AravinthPanch/araBeat/docs/ecg/MAX30003 Ultra-Low Power, Single-Channel Integrated Biopotential (ECG, R to R Detection) AFE - Maxim.pdf

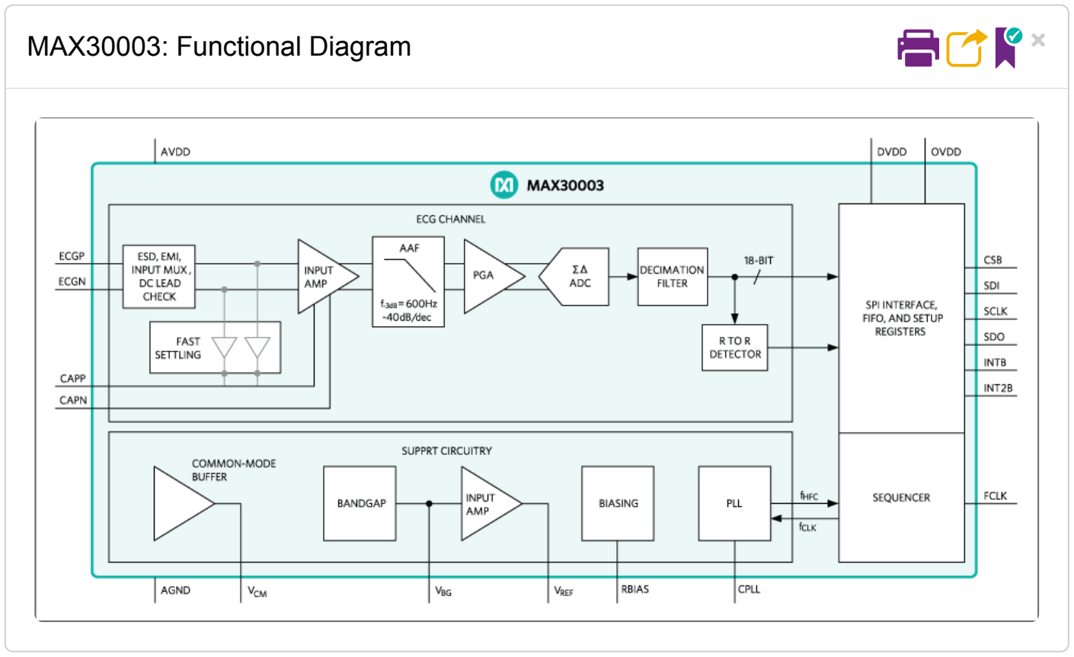
[picture p67: figure]
MAX30003: Functional Diagram
