AravinthPanch/araBeat/design/audio-rack/subwoofer-disc.jpg

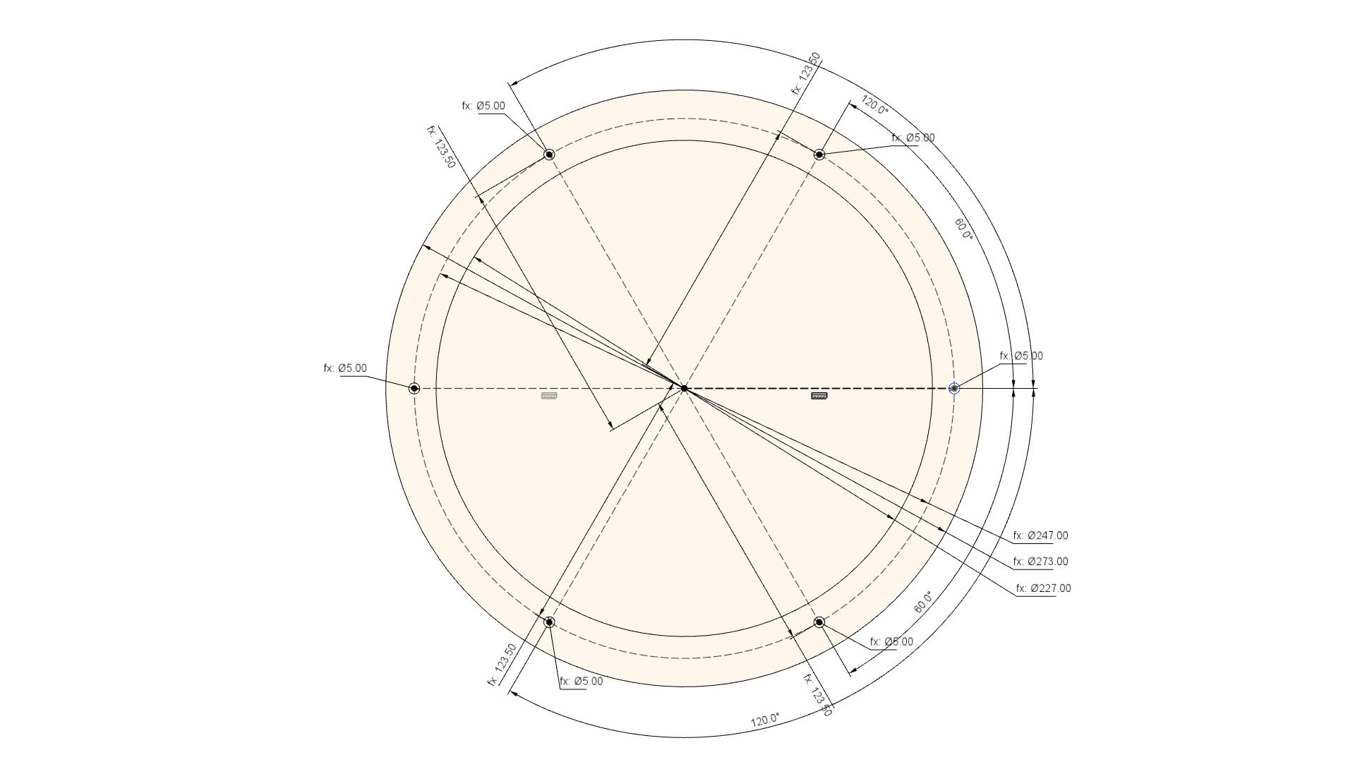
design/audio-rack/subwoofer-disc.jpg
