AravinthPanch/araBeat/design/audio-rack/tweeter-disc.jpg

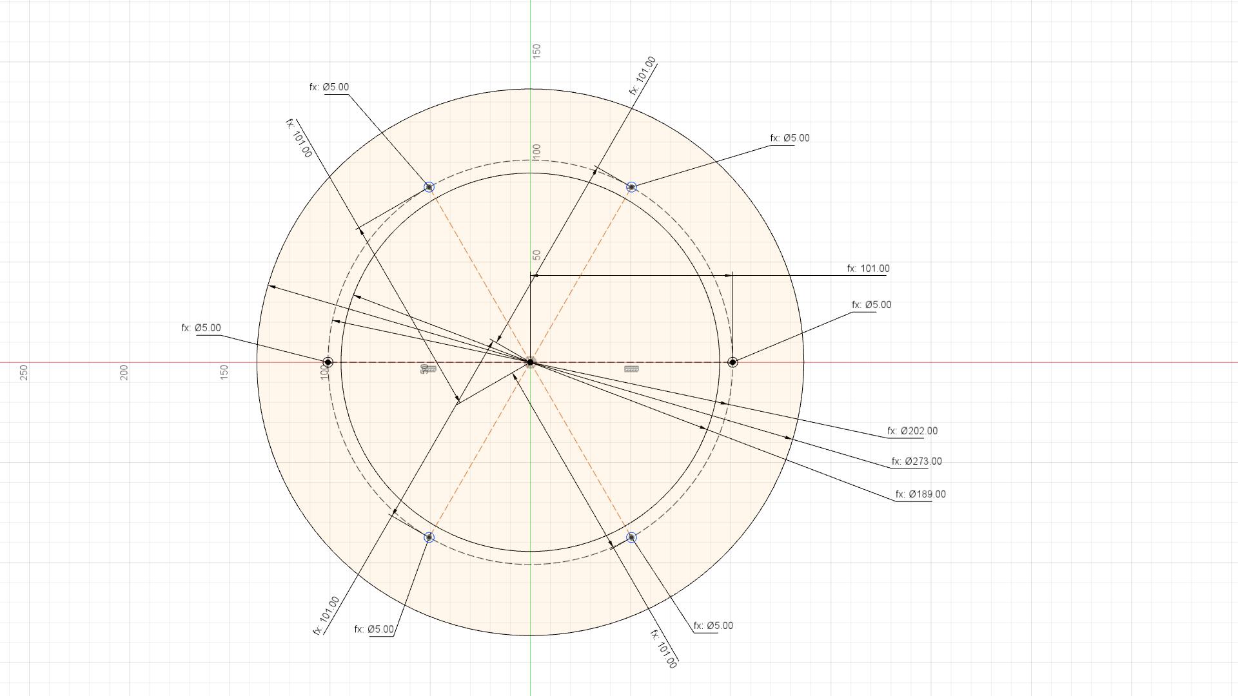
design/audio-rack/tweeter-disc.jpg
