AravinthPanch/araBeat/design/prototypes/mini-speaker-enclosure/enclosure-back.png

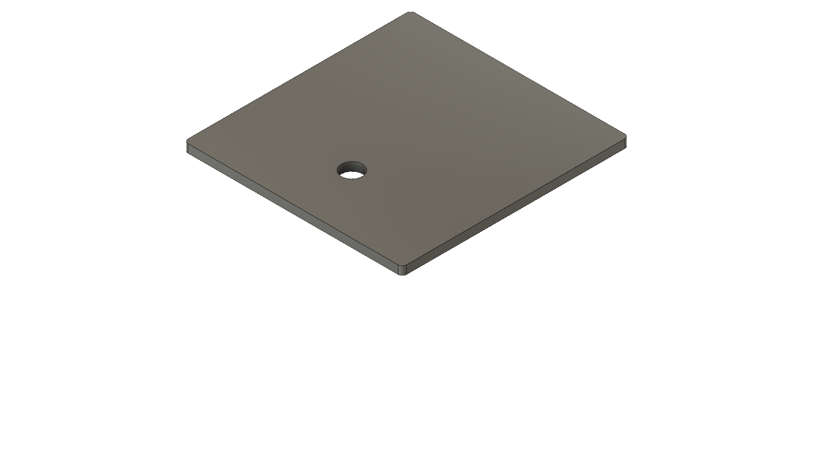
design/prototypes/mini-speaker-enclosure/enclosure-back.png
