AravinthPanch/araBeat/design/prototypes/mini-speaker-enclosure/enclosure-front.png

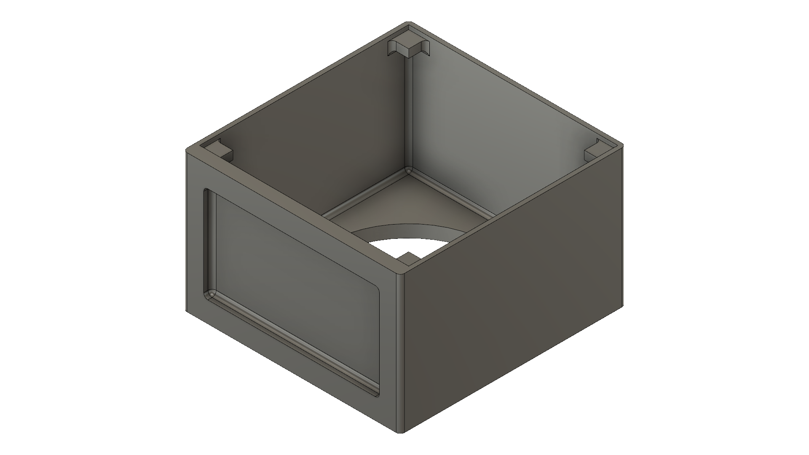
design/prototypes/mini-speaker-enclosure/enclosure-front.png
