AravinthPanch/araBeat/design/prototypes/mini-speaker-enclosure/enclosure.jpg

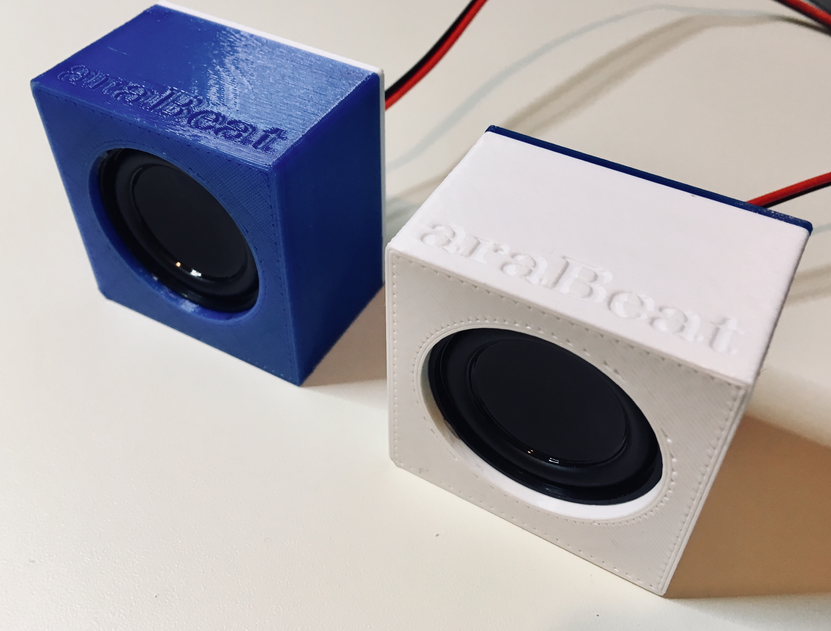
design/prototypes/mini-speaker-enclosure/enclosure.jpg
