AravinthPanch/araBeat/design/sensor-frontend/design-4-draft-chamfer/20181226_Arabeat_Draft_Hollow_preview.JPG

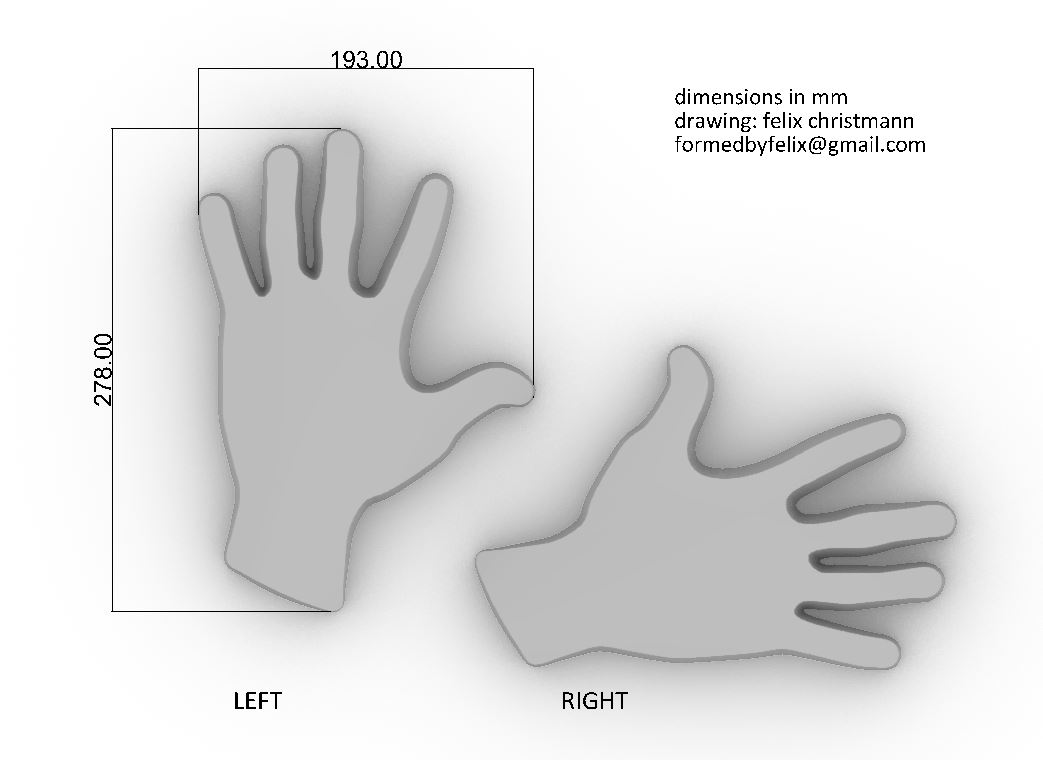
design/sensor-frontend/design-4-draft-chamfer/20181226_Arabeat_Draft_Hollow_preview.JPG
