AravinthPanch/araBeat/design/system-design/images/led-strip.png

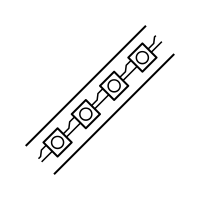
design/system-design/images/led-strip.png
