AravinthPanch/araBeat/design/system-design/system-2.png

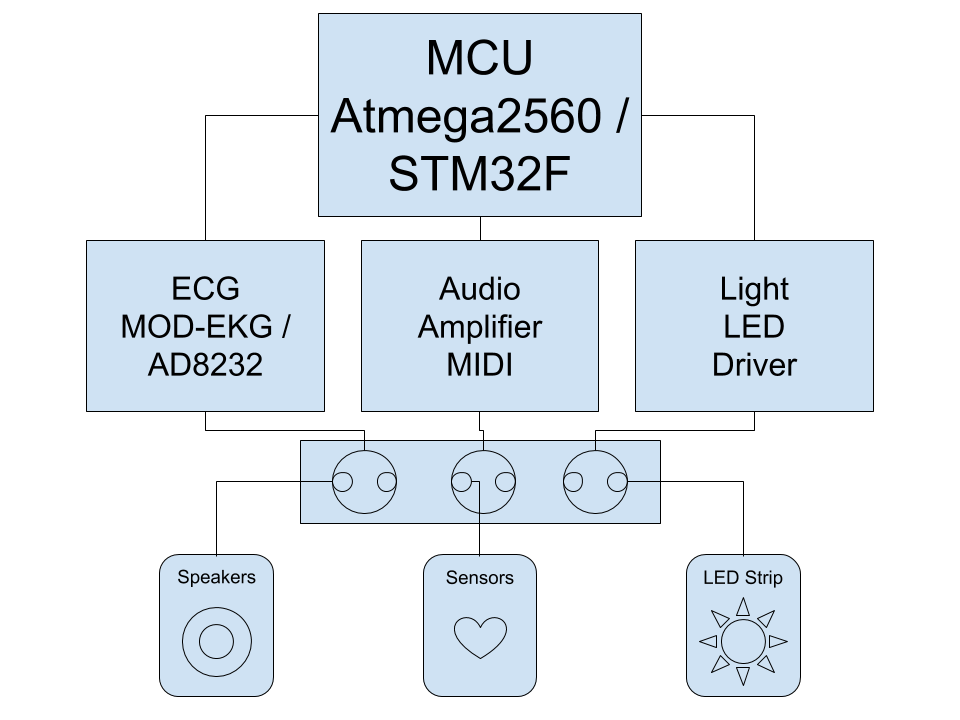
design/system-design/system-2.png
