AravinthPanch/araBeat/docs/connectors/031-203-RFX_1_SPL.jpg

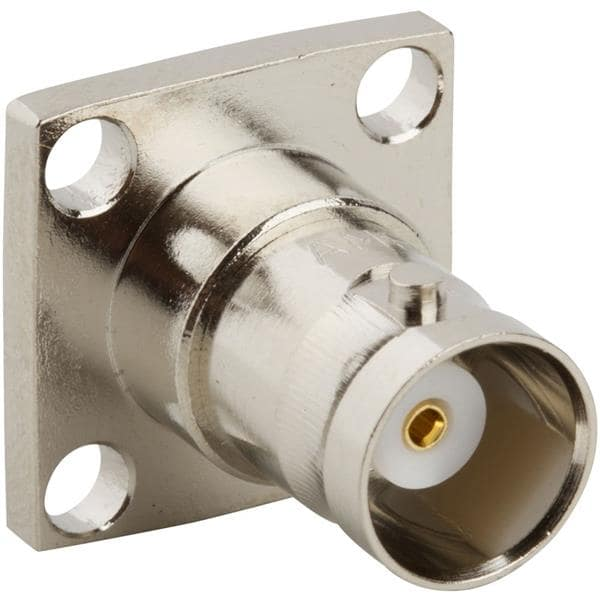
docs/connectors/031-203-RFX_1_SPL.jpg
