AravinthPanch/araBeat/docs/connectors/61caJ1zhngL._SX569_.jpg

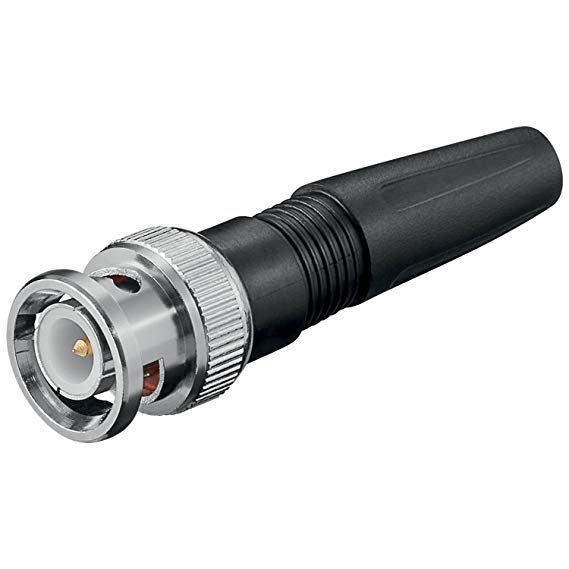
docs/connectors/61caJ1zhngL._SX569_.jpg
