AravinthPanch/araBeat/docs/connectors/BNC_RF_jack_PCB_SPL.jpg

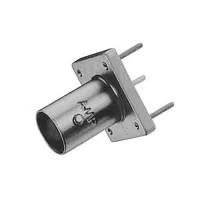
docs/connectors/BNC_RF_jack_PCB_SPL.jpg
