AravinthPanch/araBeat/docs/connectors/inhouse_vb334n_t.jpg

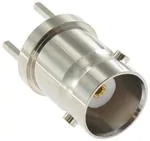
docs/connectors/inhouse_vb334n_t.jpg
