AravinthPanch/araBeat/docs/connectors/weatherproof-cable-gland-1.jpg

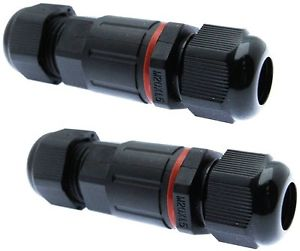
docs/connectors/weatherproof-cable-gland-1.jpg
