AravinthPanch/araBeat/docs/connectors/weatherproof-cable-gland-2.jpg

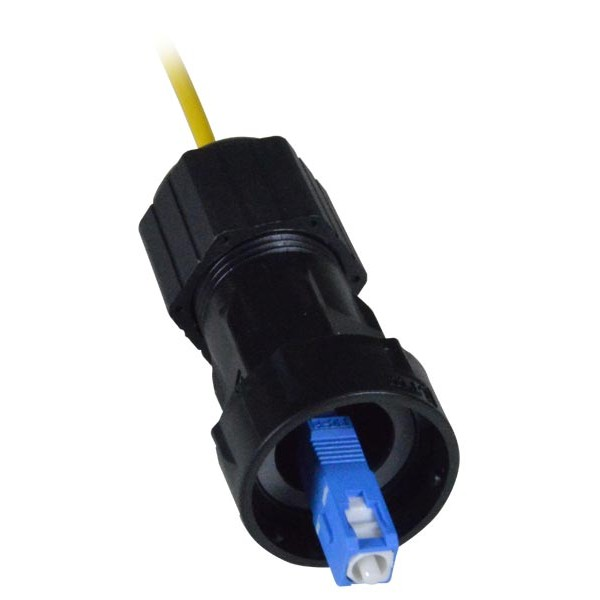
docs/connectors/weatherproof-cable-gland-2.jpg
