AravinthPanch/araBeat/docs/ecg/processing.png

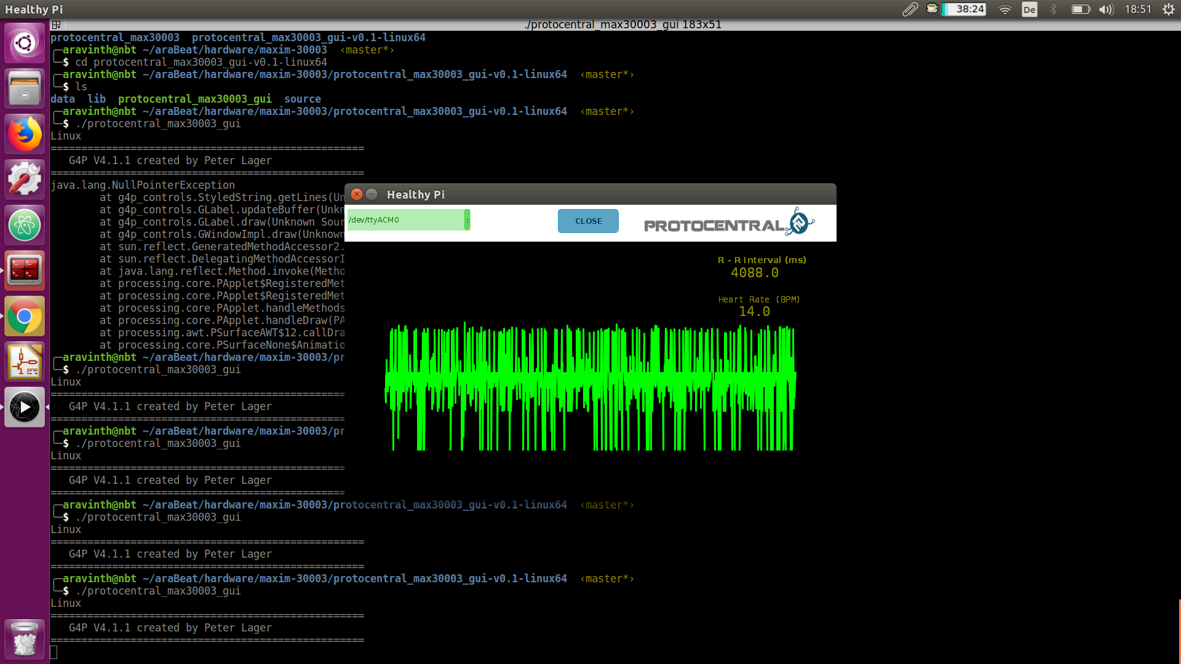
docs/ecg/processing.png
