AravinthPanch/araBeat/docs/enclosure/enclosure-1.jpg

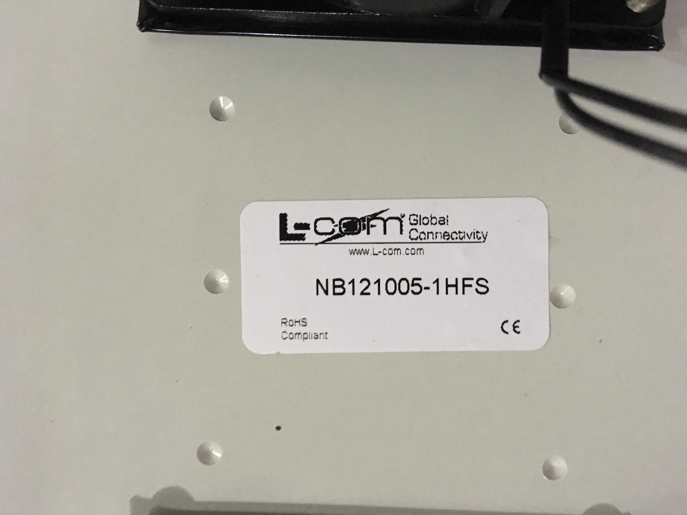
docs/enclosure/enclosure-1.jpg
