AravinthPanch/araBeat/docs/enclosure/enclosure-2.jpg

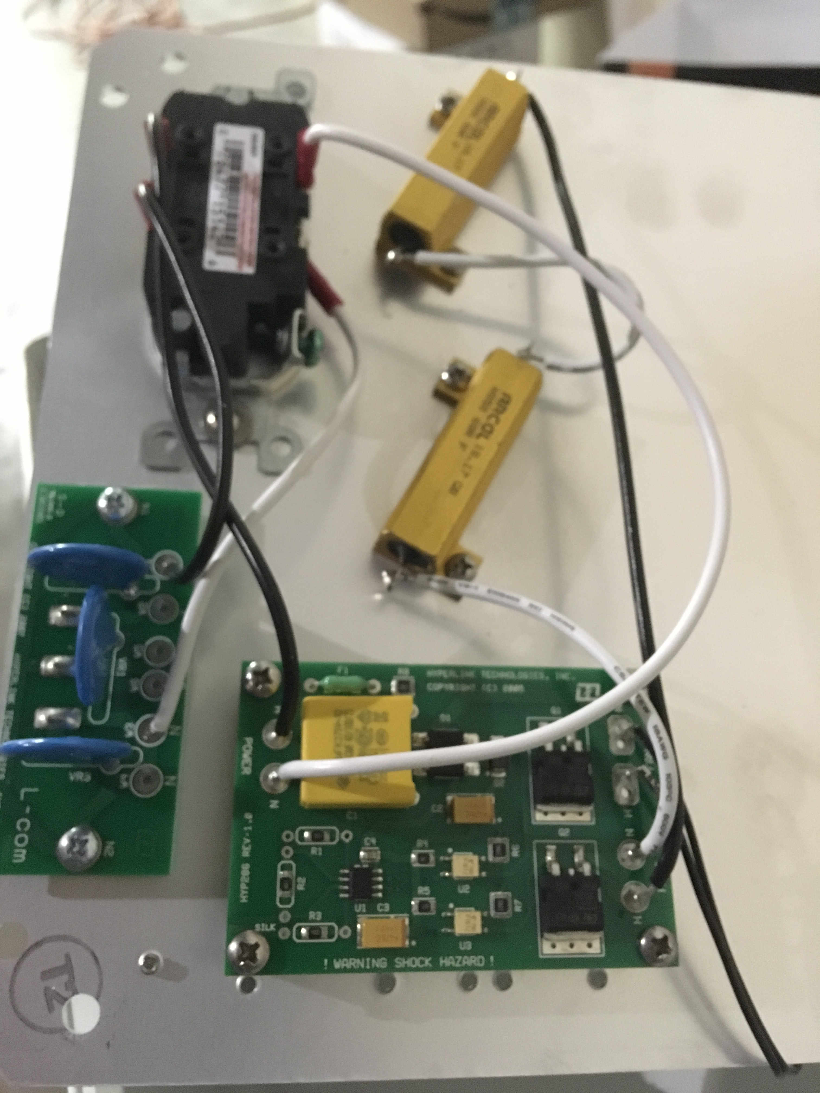
docs/enclosure/enclosure-2.jpg
