AravinthPanch/araBeat/docs/enclosure/enclosure-3.jpg

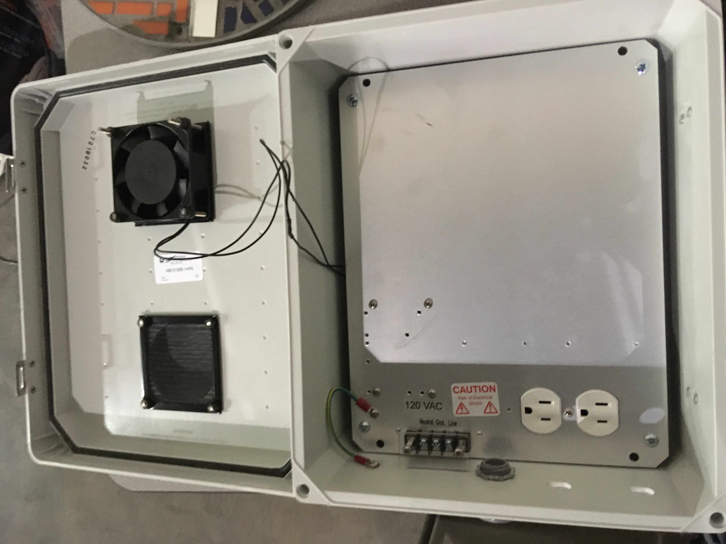
docs/enclosure/enclosure-3.jpg
