AravinthPanch/araBeat/docs/psu/linear-power.jpg

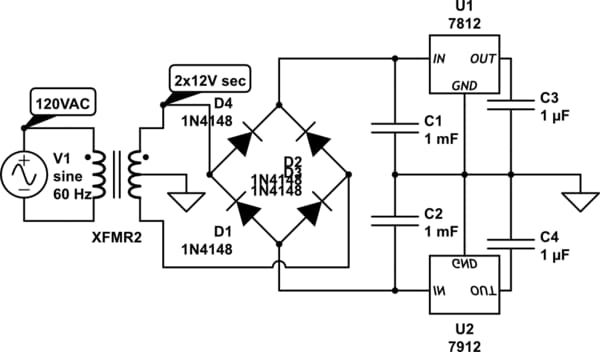
docs/psu/linear-power.jpg
