AravinthPanch/araBeat/hardware/-resources/design-rules/design-rules-1.png

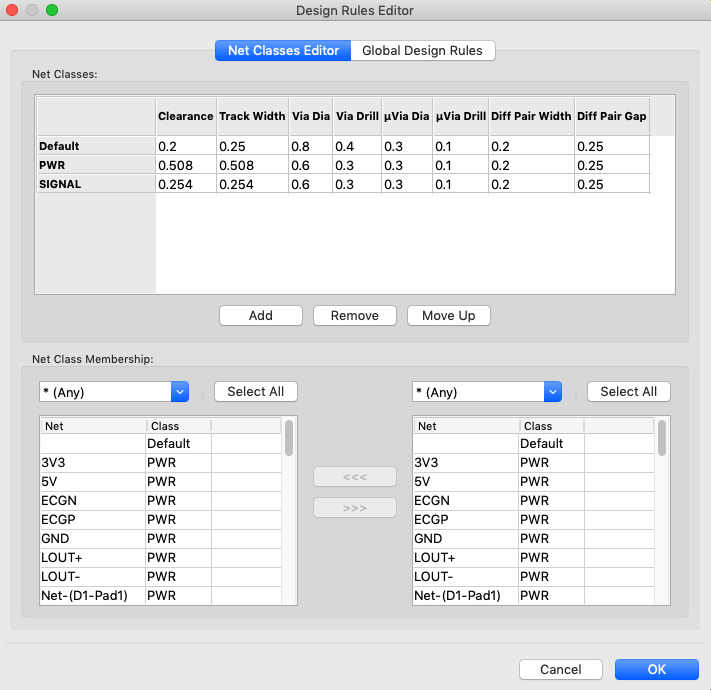
hardware/-resources/design-rules/design-rules-1.png
