AravinthPanch/araBeat/hardware/-resources/design-rules/design-rules-2.png

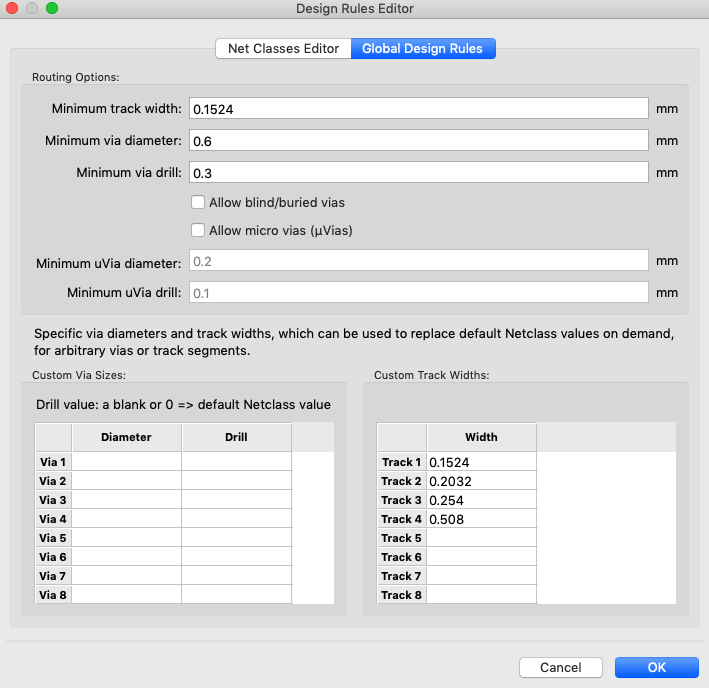
hardware/-resources/design-rules/design-rules-2.png
