AravinthPanch/araBeat/hardware/-resources/edgecut-silkscreen/inspirations/cassette-1.jpg

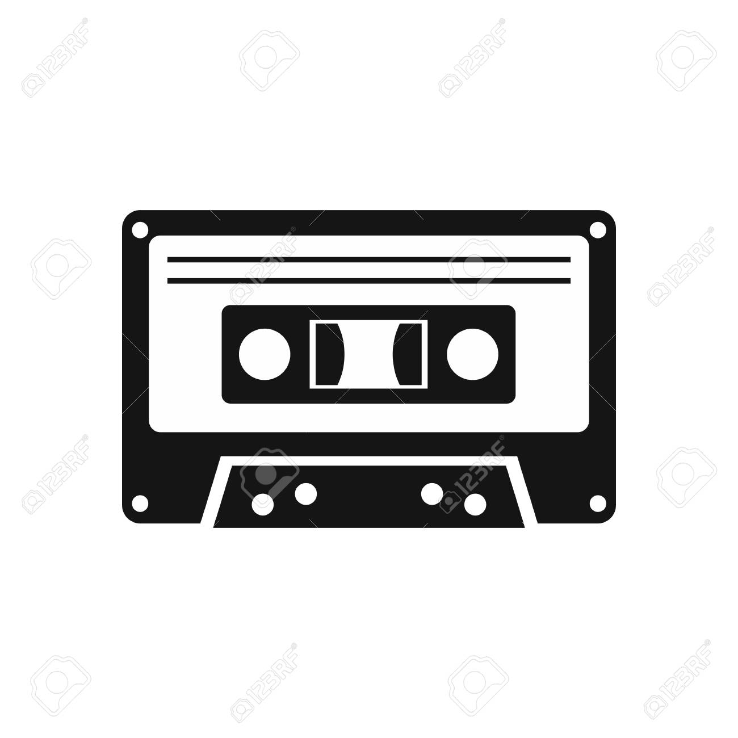
hardware/-resources/edgecut-silkscreen/inspirations/cassette-1.jpg
