AravinthPanch/araBeat/hardware/-resources/edgecut-silkscreen/inspirations/cassette-1.png

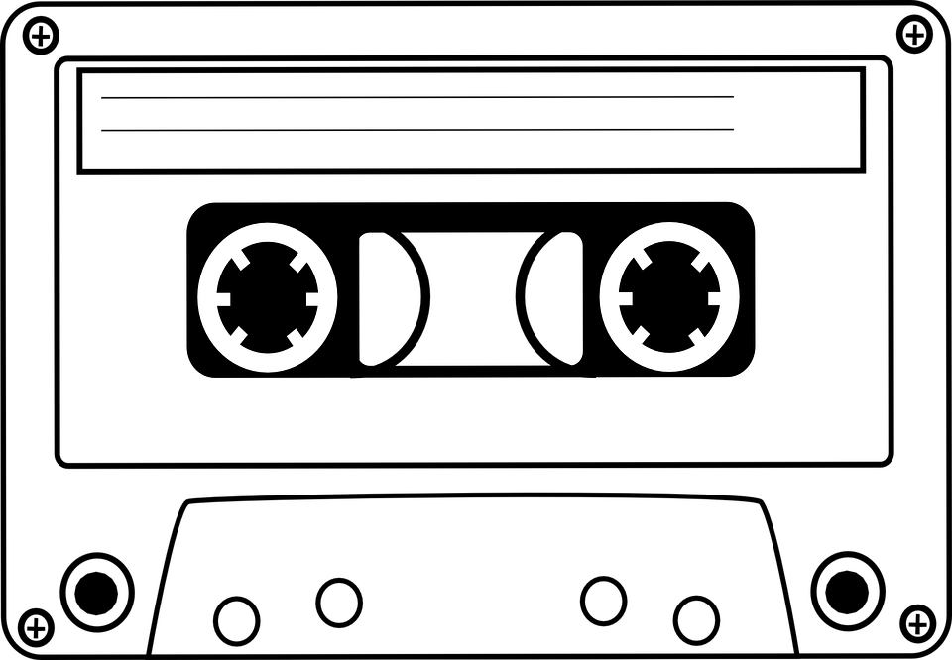
hardware/-resources/edgecut-silkscreen/inspirations/cassette-1.png
