AravinthPanch/araBeat/hardware/-resources/edgecut-silkscreen/inspirations/cassette-2.jpg

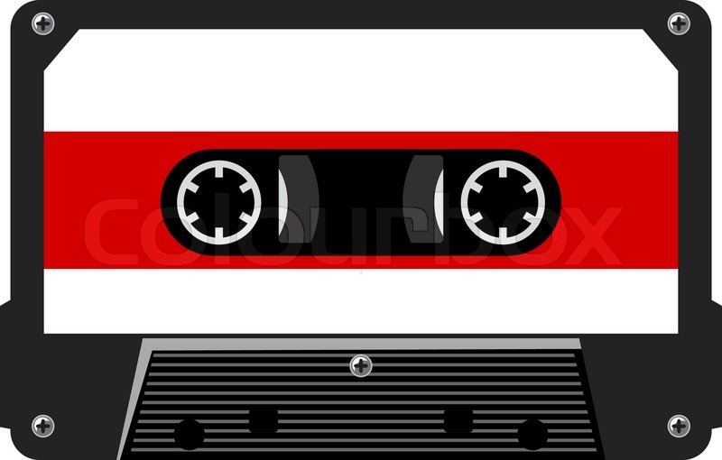
hardware/-resources/edgecut-silkscreen/inspirations/cassette-2.jpg
