AravinthPanch/araBeat/hardware/-resources/edgecut-silkscreen/inspirations/modular-1.jpg

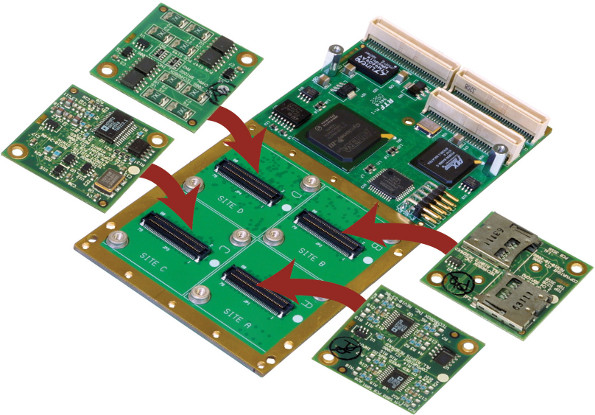
hardware/-resources/edgecut-silkscreen/inspirations/modular-1.jpg
