AravinthPanch/araBeat/hardware/-resources/edgecut-silkscreen/inspirations/modular-2.jpg

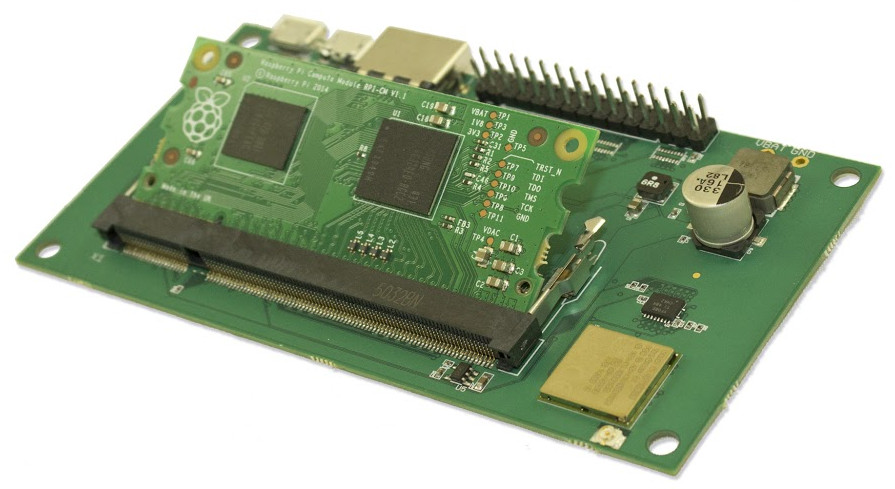
hardware/-resources/edgecut-silkscreen/inspirations/modular-2.jpg
