AravinthPanch/araBeat/hardware/-resources/edgecut-silkscreen/inspirations/modular-3.jpg

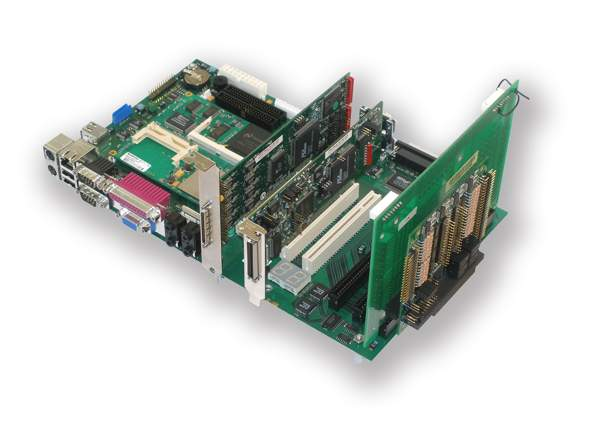
hardware/-resources/edgecut-silkscreen/inspirations/modular-3.jpg
