AravinthPanch/araBeat/hardware/-resources/edgecut-silkscreen/inspirations/retro-console-1.jpg

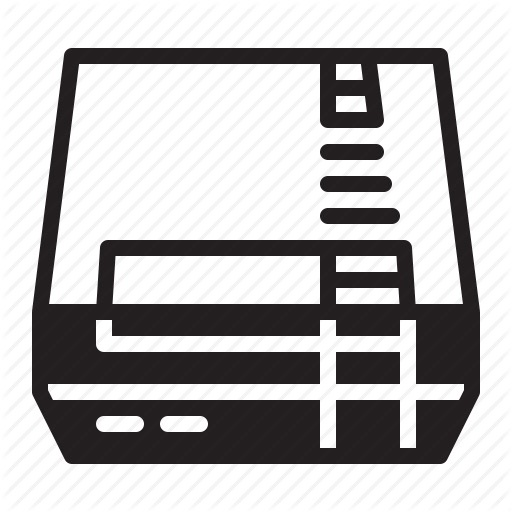
hardware/-resources/edgecut-silkscreen/inspirations/retro-console-1.jpg
