AravinthPanch/araBeat/hardware/-resources/edgecut-silkscreen/inspirations/retro-console-2.jpg

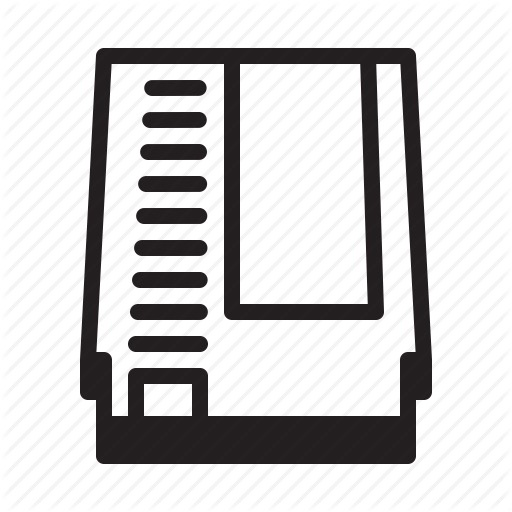
hardware/-resources/edgecut-silkscreen/inspirations/retro-console-2.jpg
