AravinthPanch/araBeat/hardware/-resources/edgecut-silkscreen/inspirations/retro-console-3.jpg

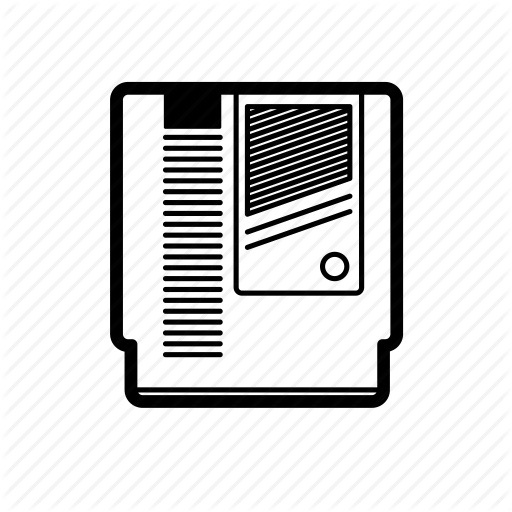
hardware/-resources/edgecut-silkscreen/inspirations/retro-console-3.jpg
