AravinthPanch/araBeat/hardware/-resources/edgecut-silkscreen/inspirations/retro-console-4.jpg

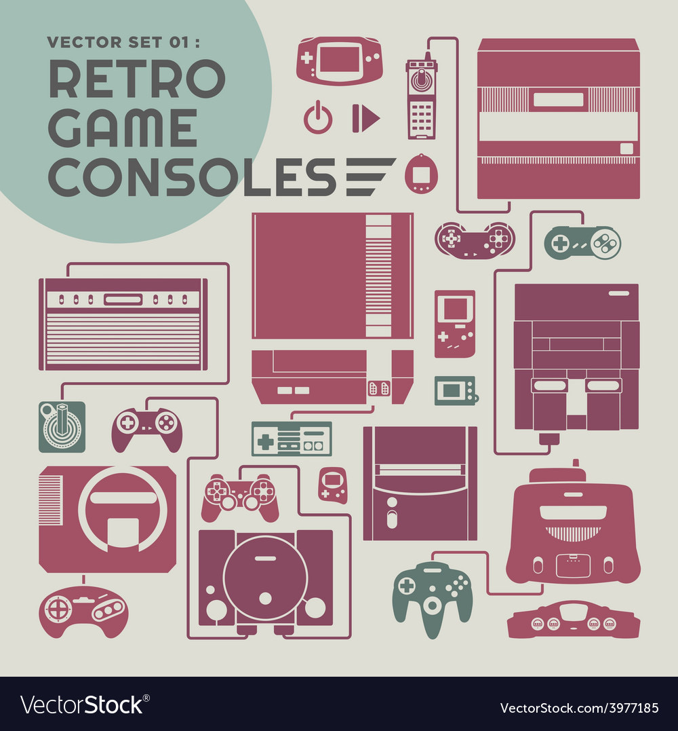
hardware/-resources/edgecut-silkscreen/inspirations/retro-console-4.jpg
