AravinthPanch/araBeat/hardware/-resources/edgecut-silkscreen/inspirations/retro-console-5.jpg

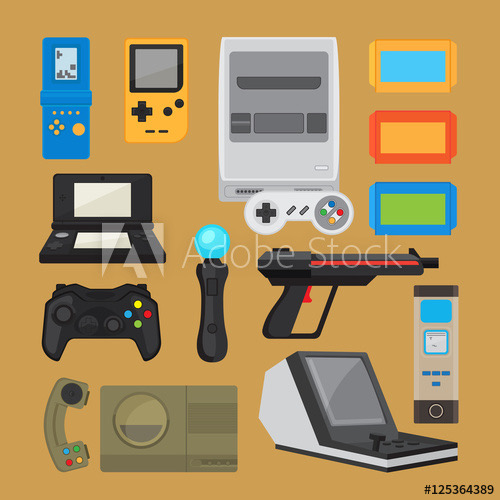
hardware/-resources/edgecut-silkscreen/inspirations/retro-console-5.jpg
