AravinthPanch/araBeat/hardware/-resources/edgecut-silkscreen/inspirations/retro-console-6.jpg

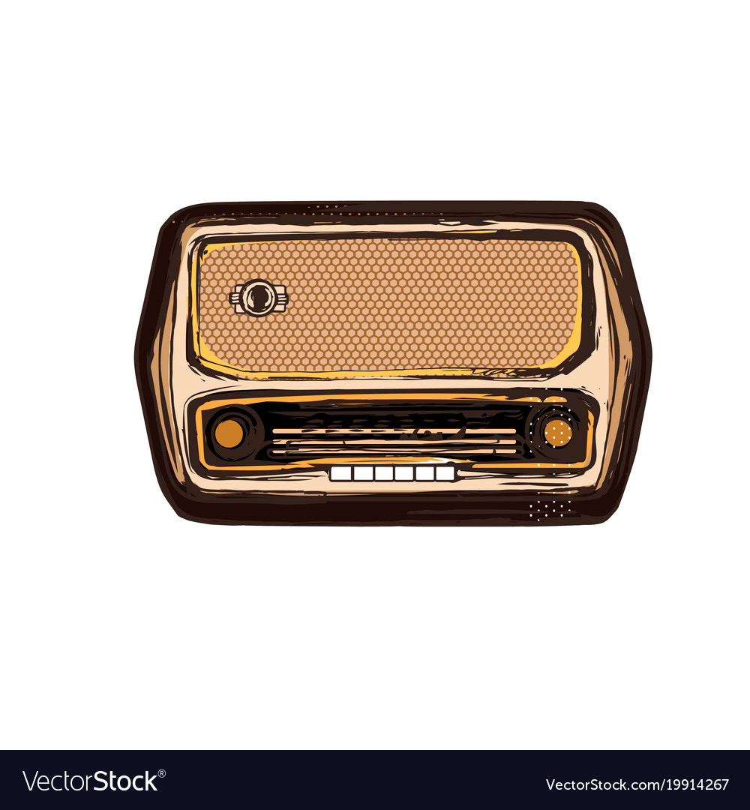
hardware/-resources/edgecut-silkscreen/inspirations/retro-console-6.jpg
