AravinthPanch/araBeat/hardware/-resources/edgecut-silkscreen/inspirations/retro-console-7.jpg

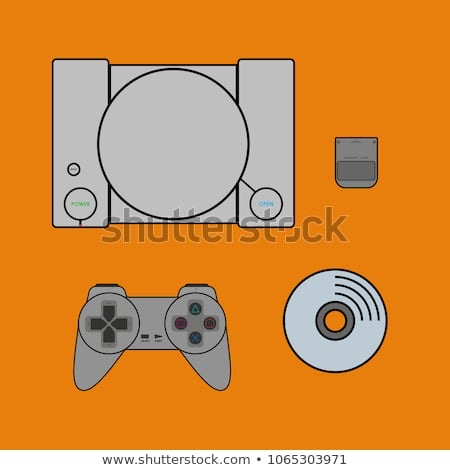
hardware/-resources/edgecut-silkscreen/inspirations/retro-console-7.jpg
