AravinthPanch/araBeat/hardware/-resources/misc/smd-footprint.png

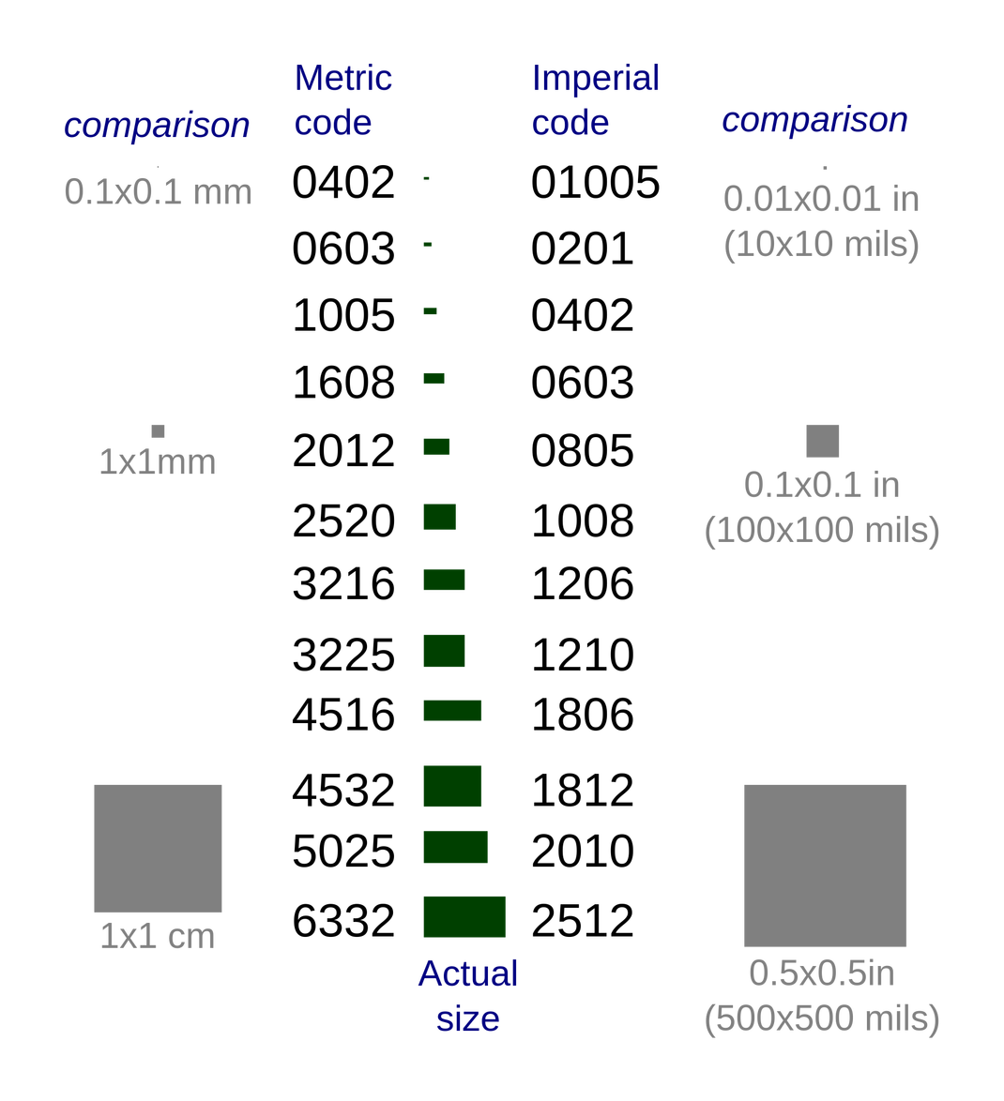
hardware/-resources/misc/smd-footprint.png
