AravinthPanch/araBeat/hardware/-resources/pinout/arduino-nano-pinout.png

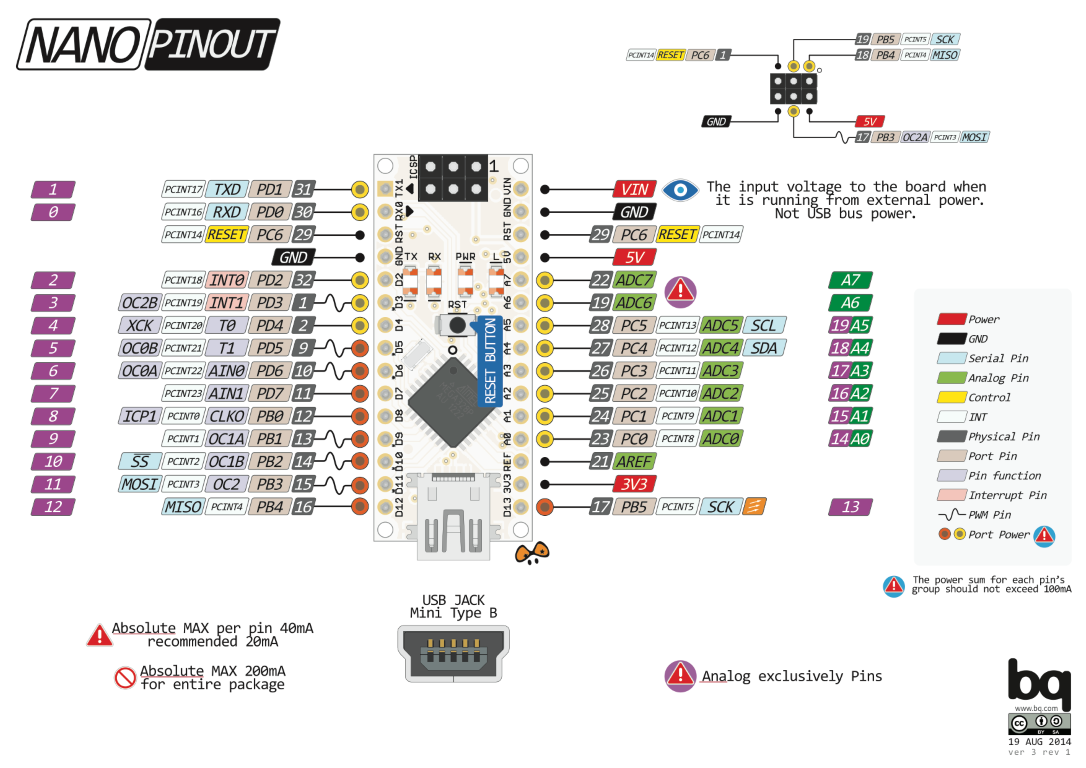
hardware/-resources/pinout/arduino-nano-pinout.png
