AravinthPanch/araBeat/hardware/-resources/pinout/dsp.png

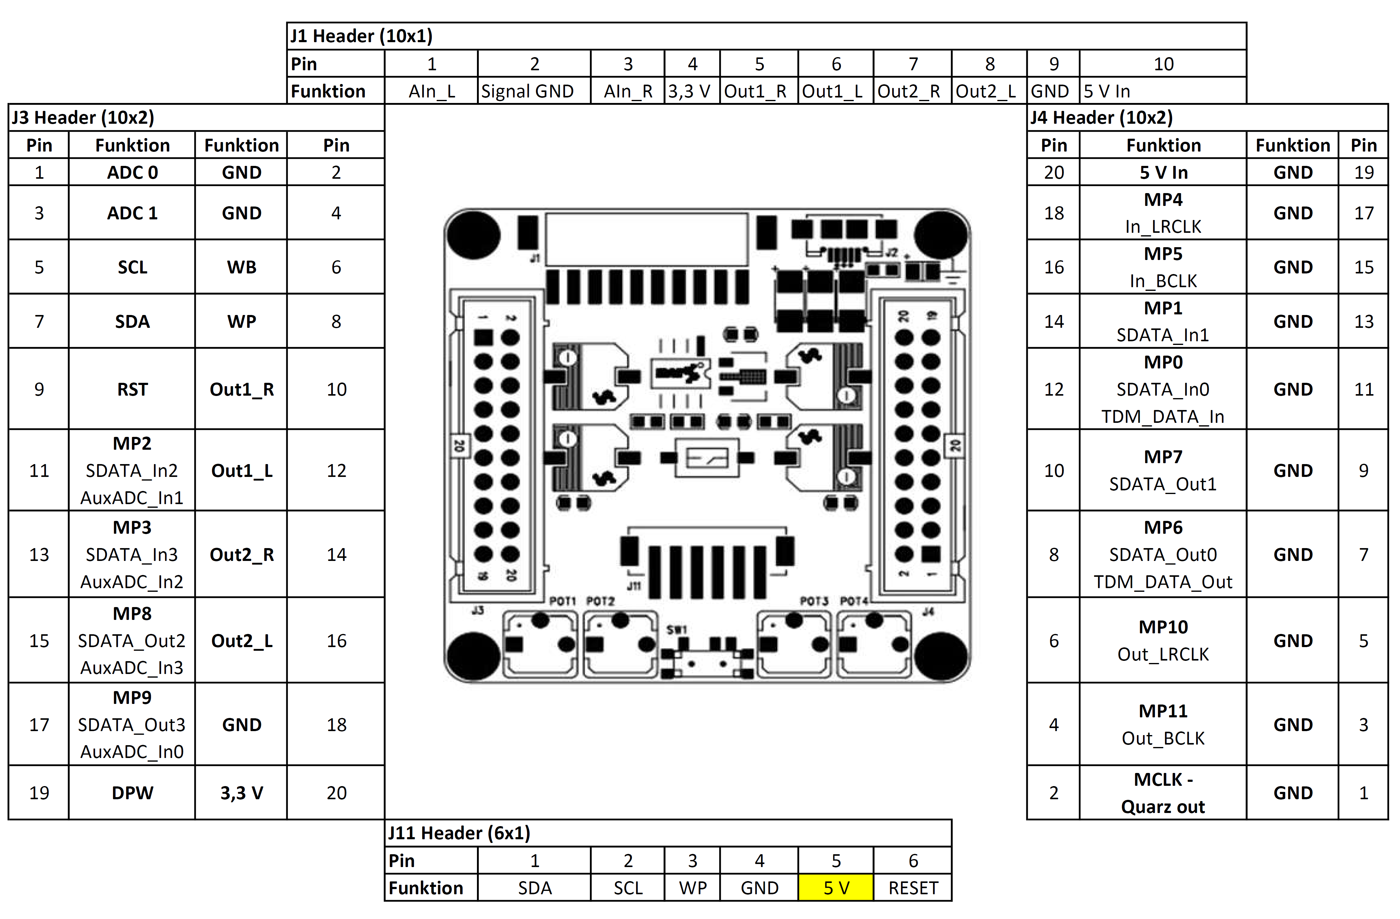
hardware/-resources/pinout/dsp.png
