AravinthPanch/araBeat/hardware/-resources/pinout/rca-interface.png

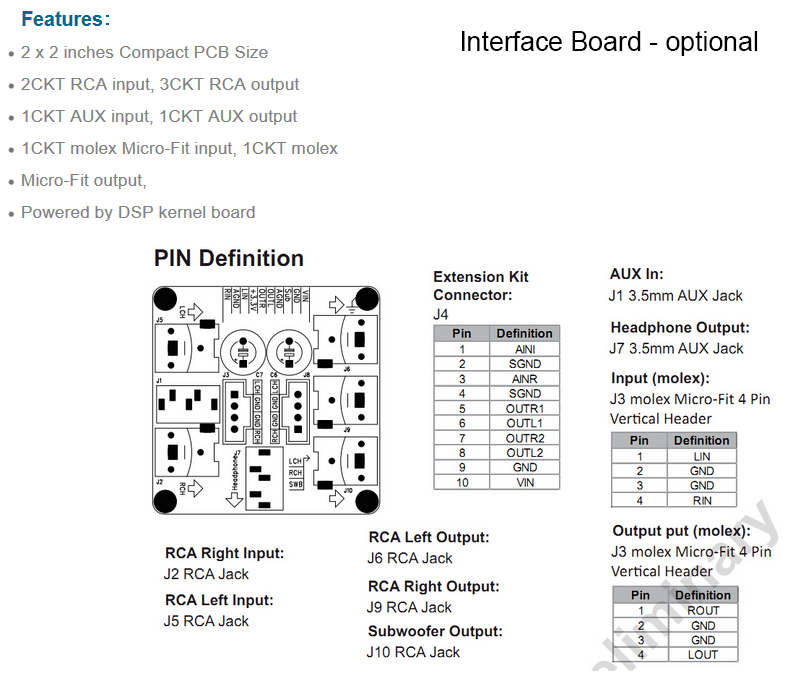
hardware/-resources/pinout/rca-interface.png
