AravinthPanch/araBeat/hardware/-resources/seeed-dfm/gerber-1.png

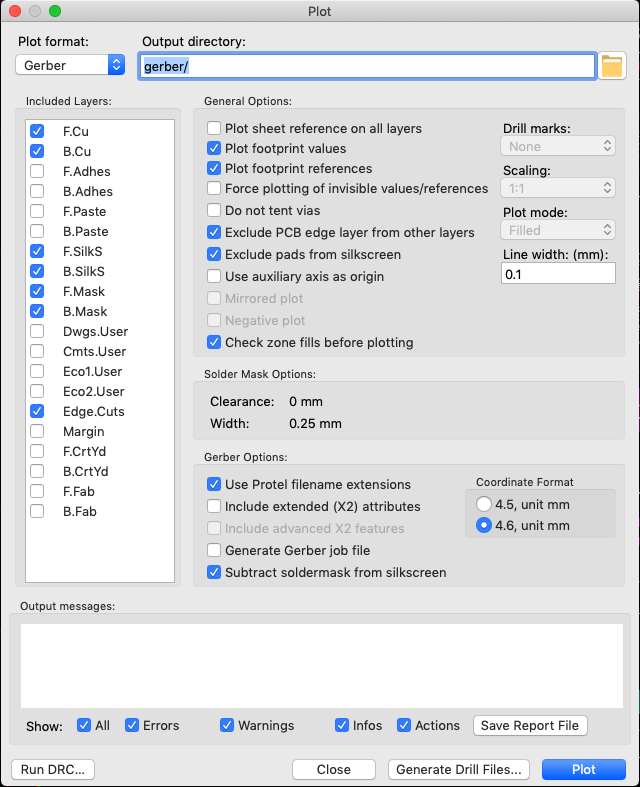
hardware/-resources/seeed-dfm/gerber-1.png
