AravinthPanch/araBeat/hardware/-resources/seeed-dfm/gerber-2.png

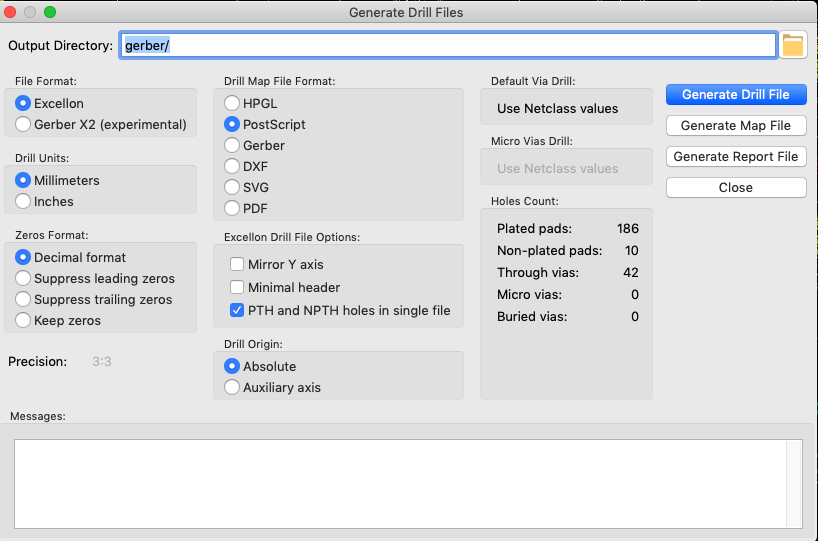
hardware/-resources/seeed-dfm/gerber-2.png
