AravinthPanch/araBeat/images/audio/audio-1.jpg

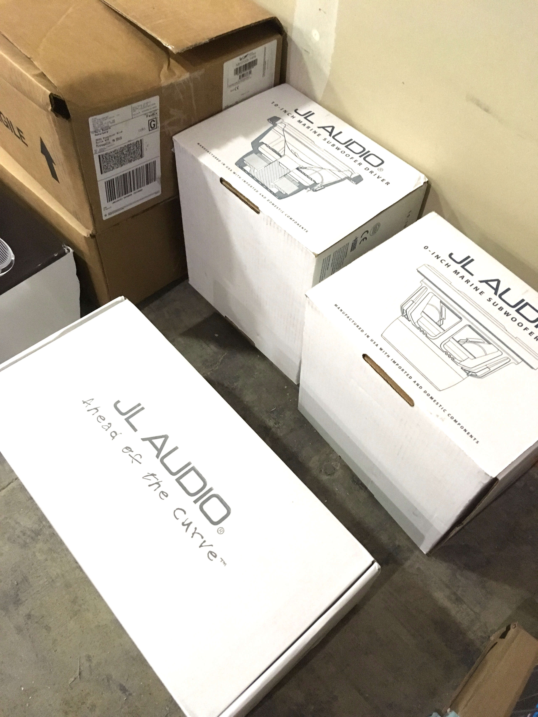
images/audio/audio-1.jpg
