AravinthPanch/araBeat/images/audio/audio-2.jpg

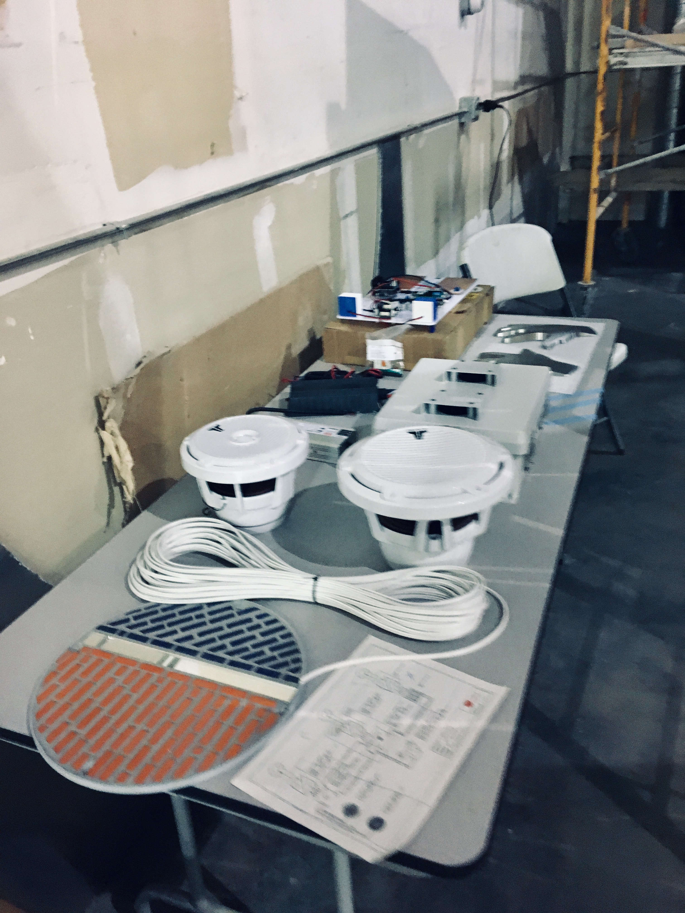
images/audio/audio-2.jpg
