AravinthPanch/araBeat/images/audio/speaker-rack-1.jpg

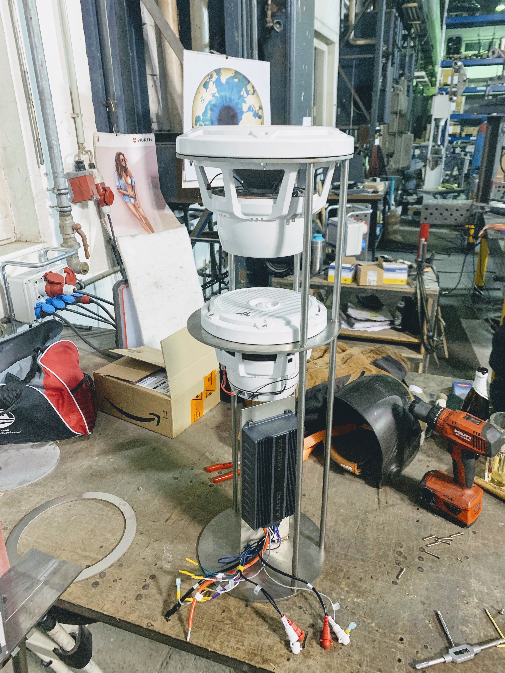
images/audio/speaker-rack-1.jpg
