AravinthPanch/araBeat/images/audio/wondom-dsp-4.jpg

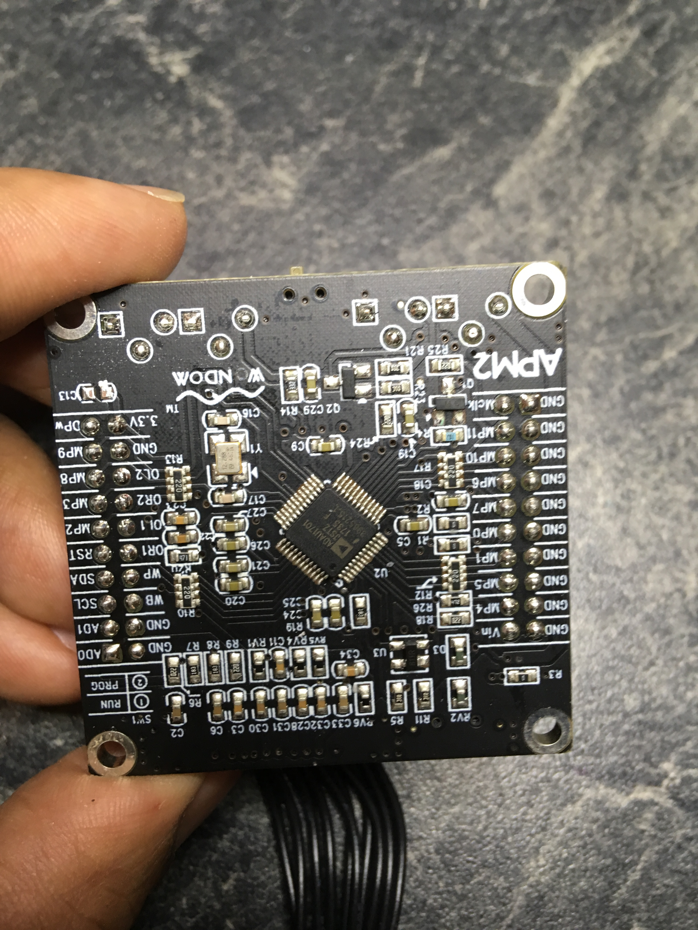
images/audio/wondom-dsp-4.jpg
