AravinthPanch/araBeat/images/behind-the-scenes/lighting.png

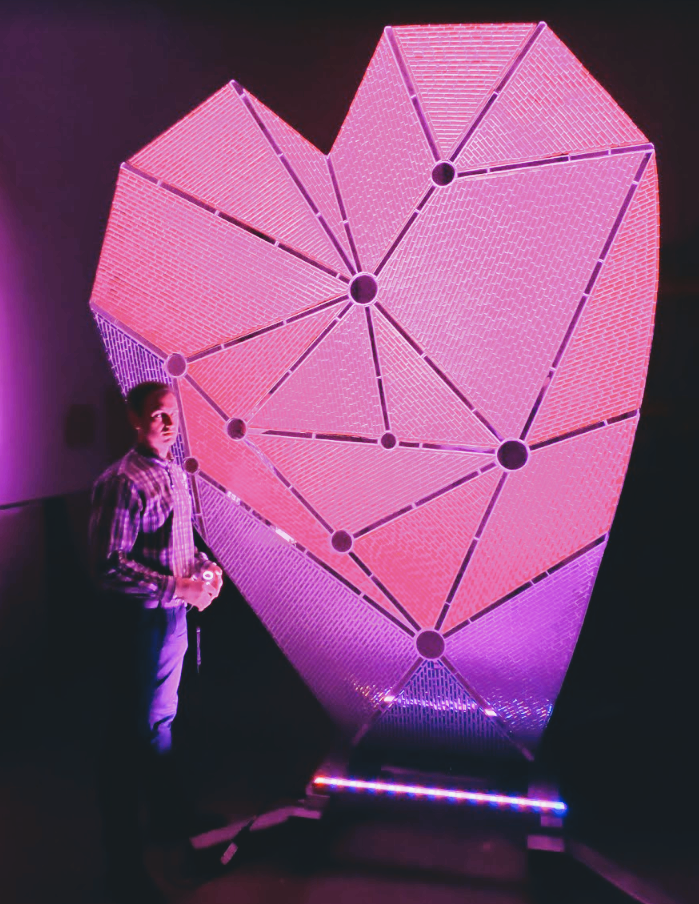
images/behind-the-scenes/lighting.png
