AravinthPanch/araBeat/images/behind-the-scenes/stacia-mosaic-1.jpg

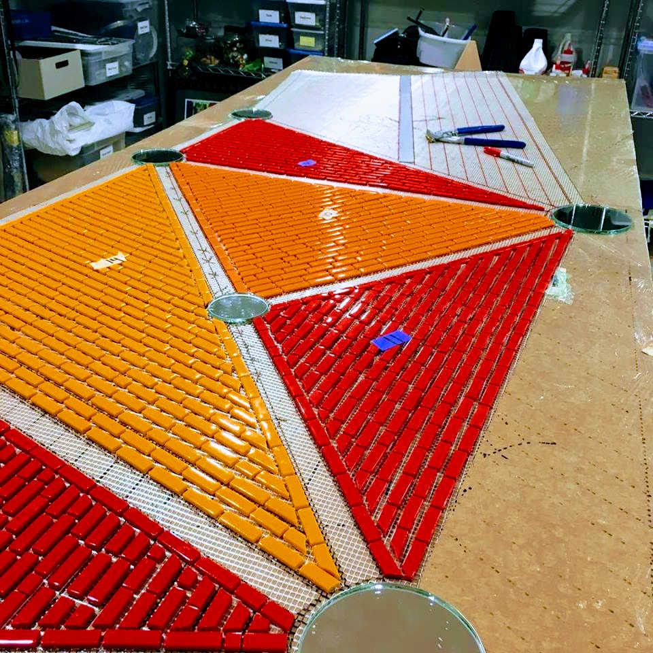
images/behind-the-scenes/stacia-mosaic-1.jpg
