AravinthPanch/araBeat/images/behind-the-scenes/stacia-mosaic-2.jpg

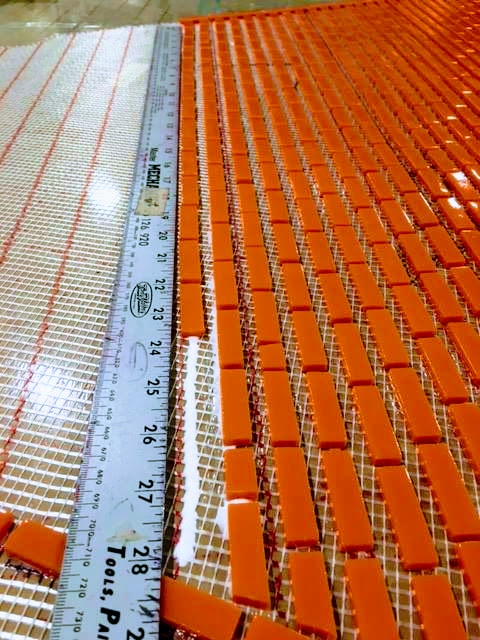
images/behind-the-scenes/stacia-mosaic-2.jpg
