AravinthPanch/araBeat/images/behind-the-scenes/stacia-mosaic-5.jpg

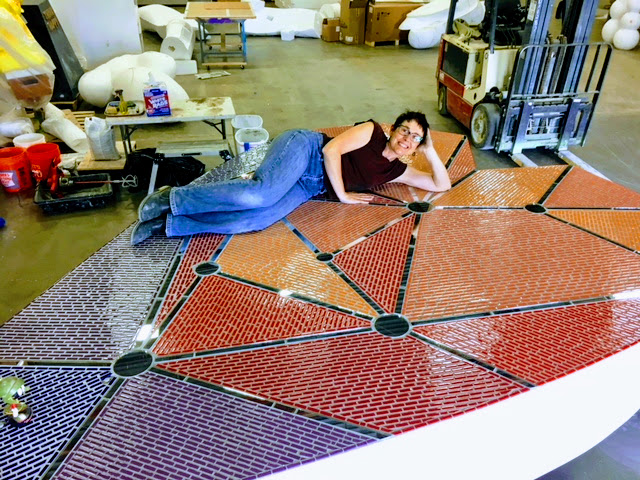
images/behind-the-scenes/stacia-mosaic-5.jpg
