AravinthPanch/araBeat/images/behind-the-scenes/tivoli.jpg

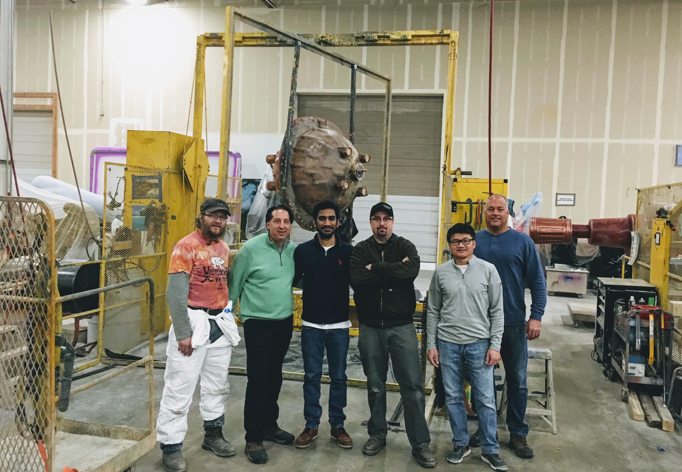
images/behind-the-scenes/tivoli.jpg
