AravinthPanch/araBeat/images/chambers/chamber-2.jpg

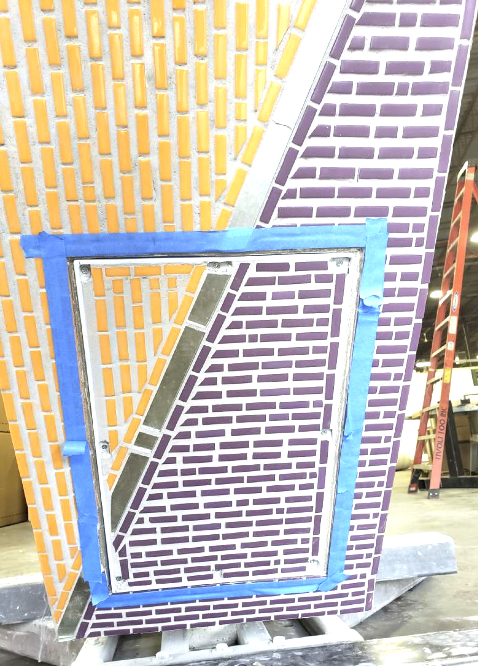
images/chambers/chamber-2.jpg
