AravinthPanch/araBeat/images/final/2021-3-29-1.jpg

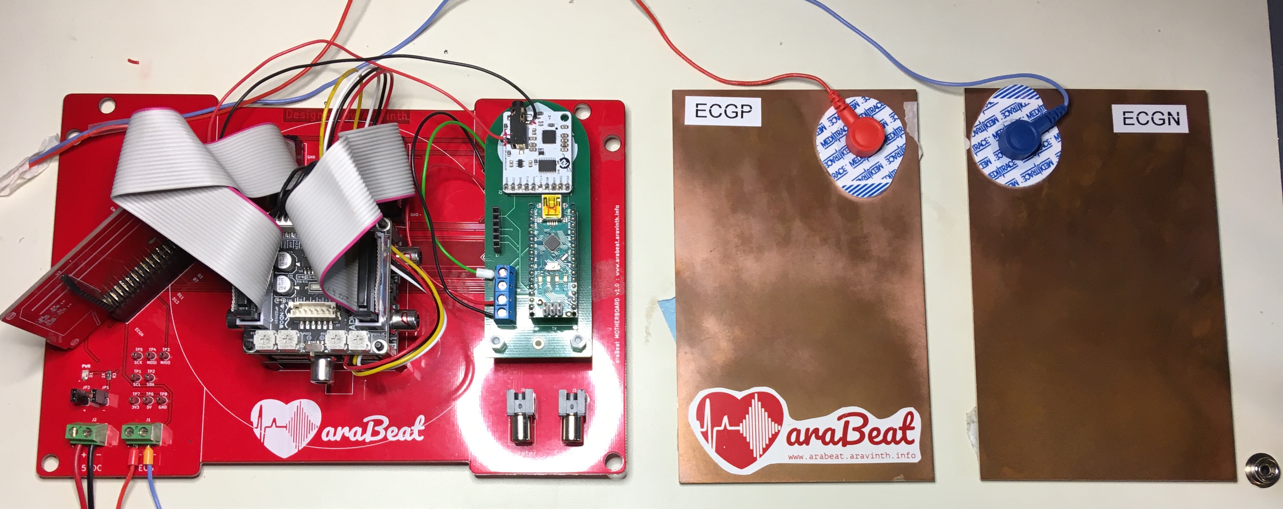
images/final/2021-3-29-1.jpg
