AravinthPanch/araBeat/images/final/2021-3-29-2.jpg

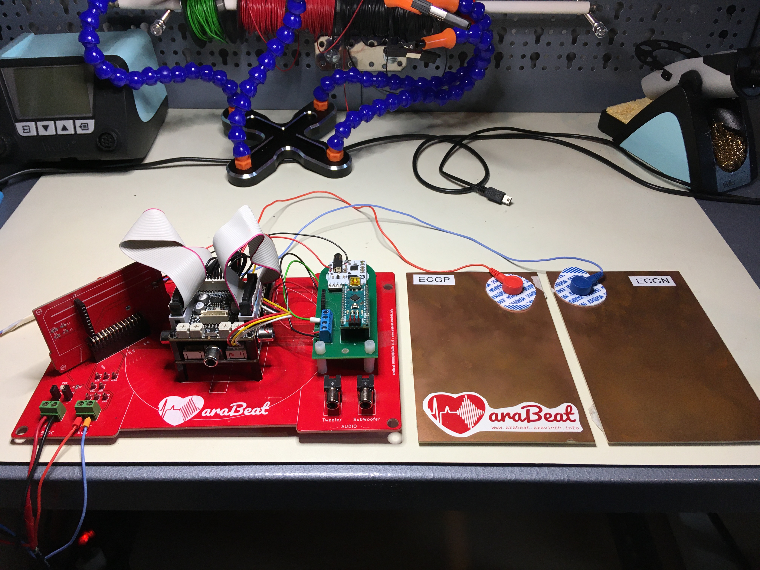
images/final/2021-3-29-2.jpg
