AravinthPanch/araBeat/images/final/2021-3-29-4.jpg

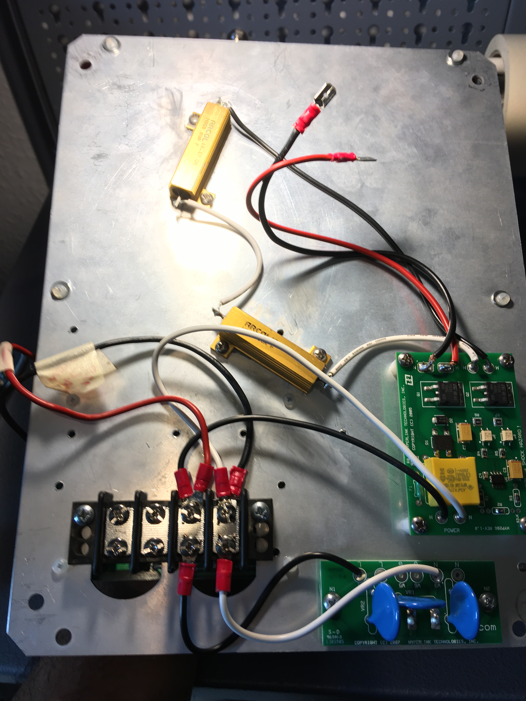
images/final/2021-3-29-4.jpg
