AravinthPanch/araBeat/images/final/2021-3-29-5.jpg

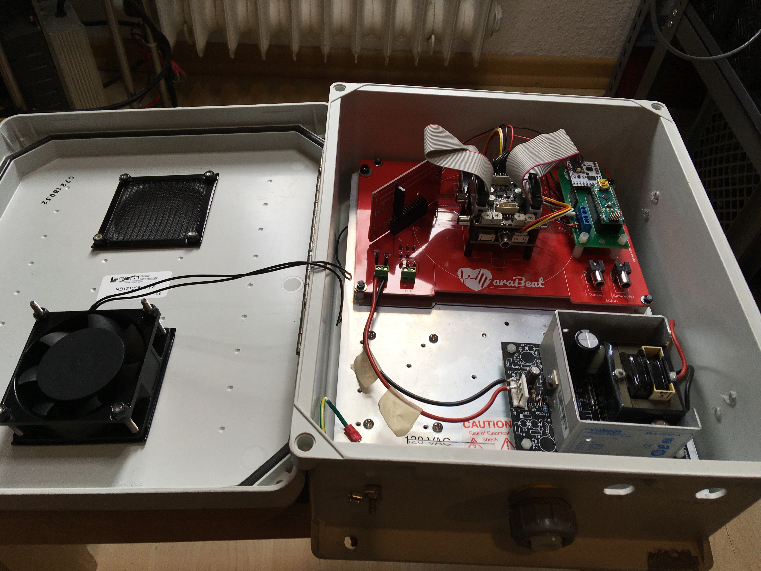
images/final/2021-3-29-5.jpg
