AravinthPanch/araBeat/images/final/2021-3-29-7.jpg

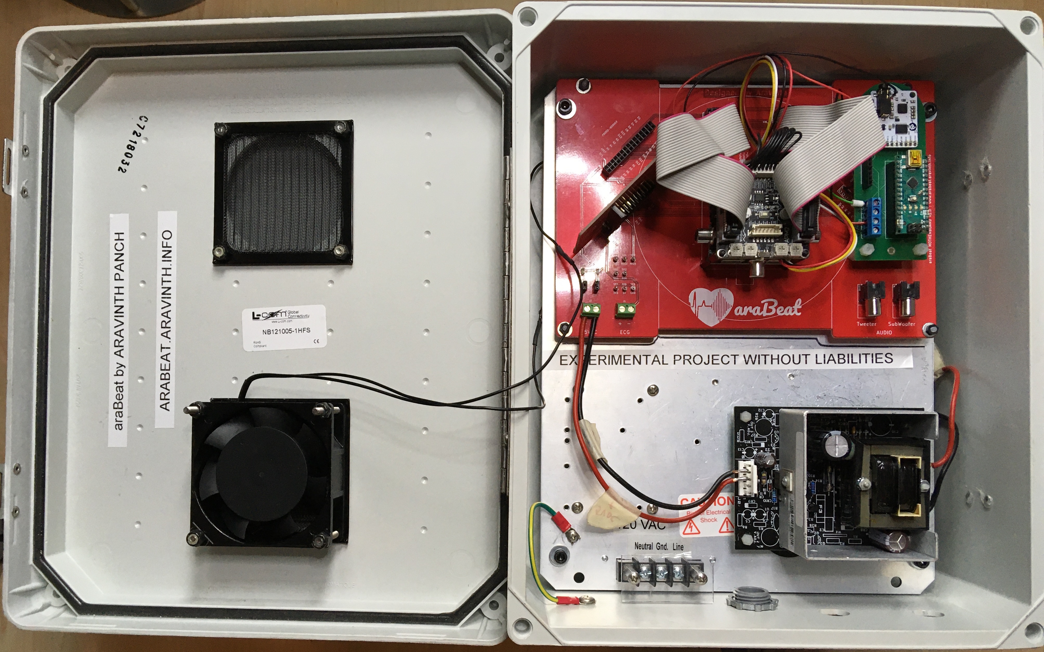
images/final/2021-3-29-7.jpg
