AravinthPanch/araBeat/images/final/2021-3-29-8.jpg

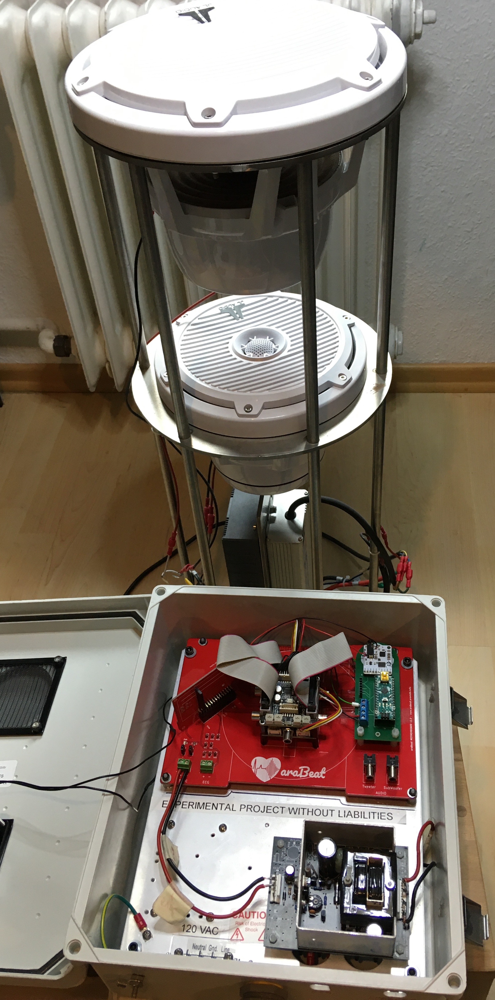
images/final/2021-3-29-8.jpg
