AravinthPanch/araBeat/images/final/2021-3-29-9.jpg

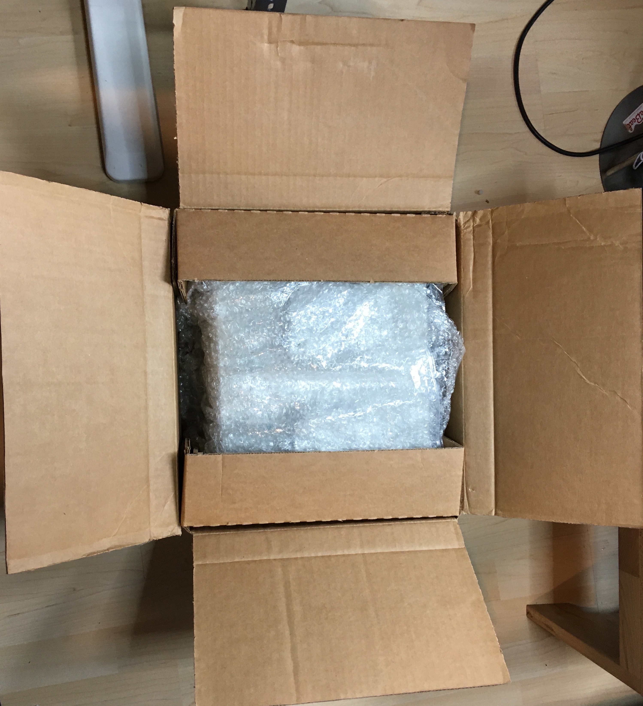
images/final/2021-3-29-9.jpg
