AravinthPanch/araBeat/images/final/2021-3-29-10.jpg

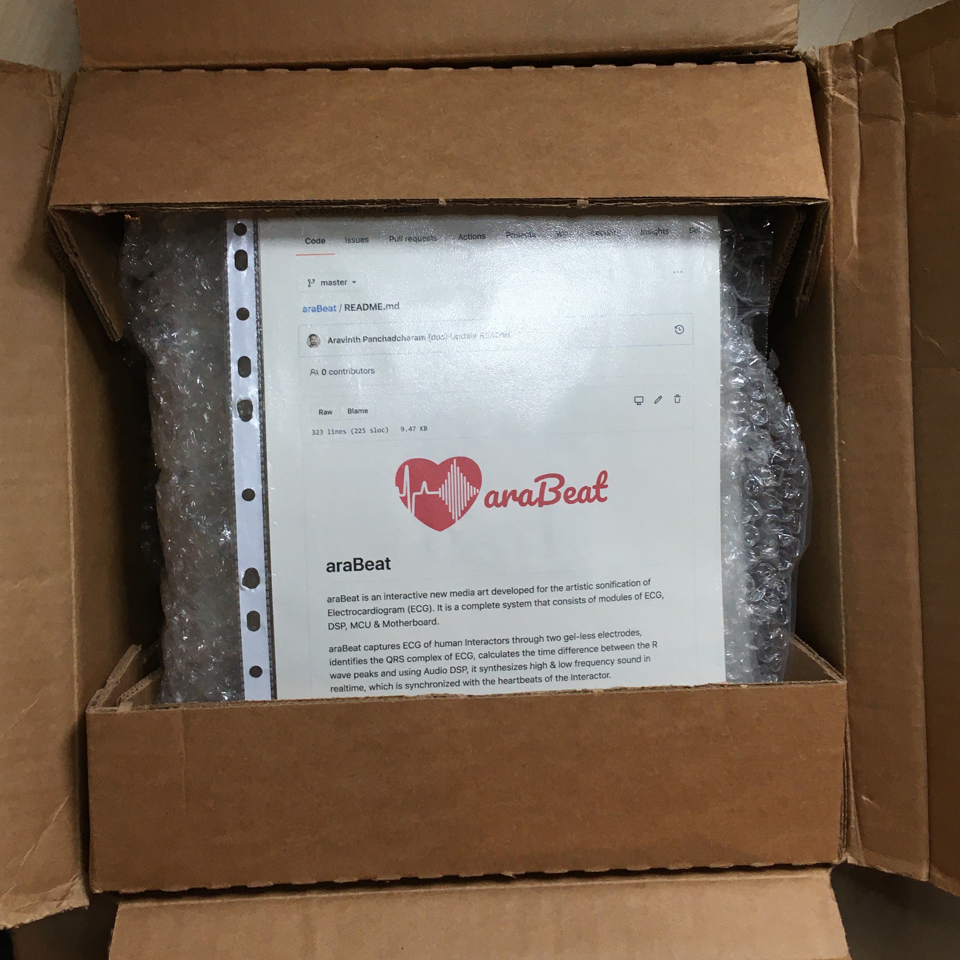
images/final/2021-3-29-10.jpg
