AravinthPanch/araBeat/images/pcbs/arabeat-v1.0-2.jpg

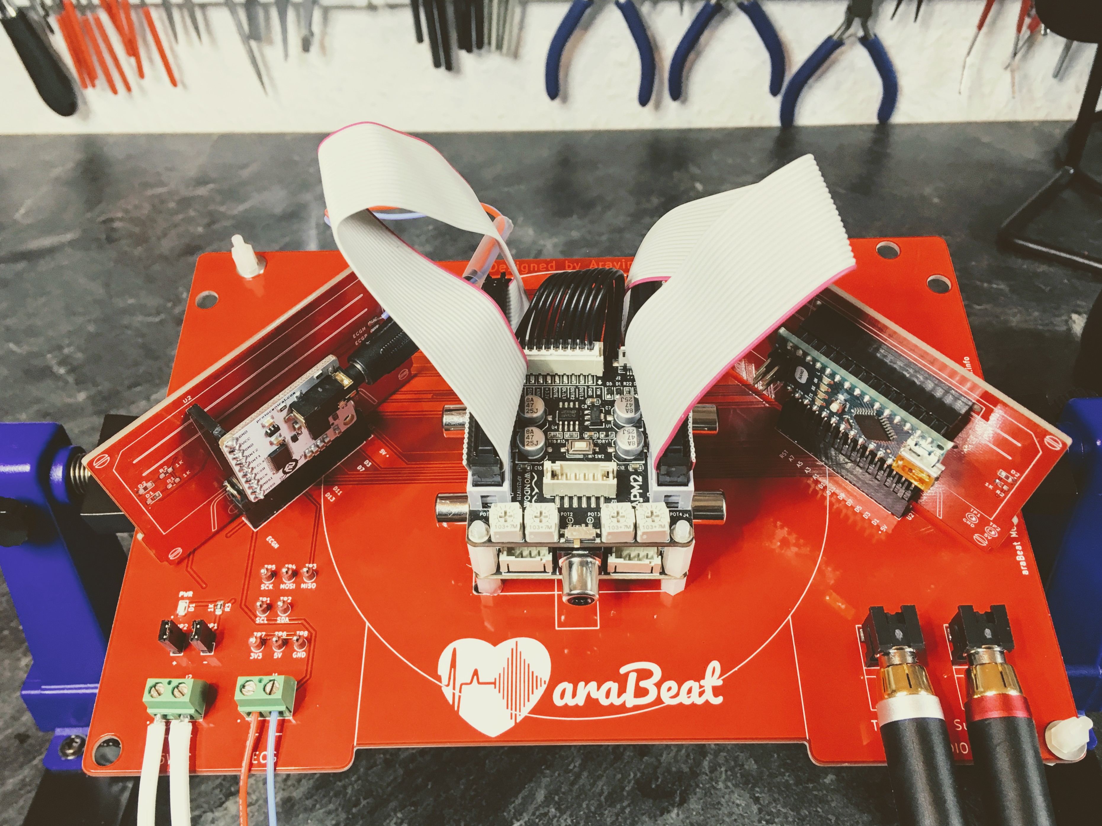
images/pcbs/arabeat-v1.0-2.jpg
