AravinthPanch/araBeat/images/pcbs/arabeat-v1.0-3.jpg

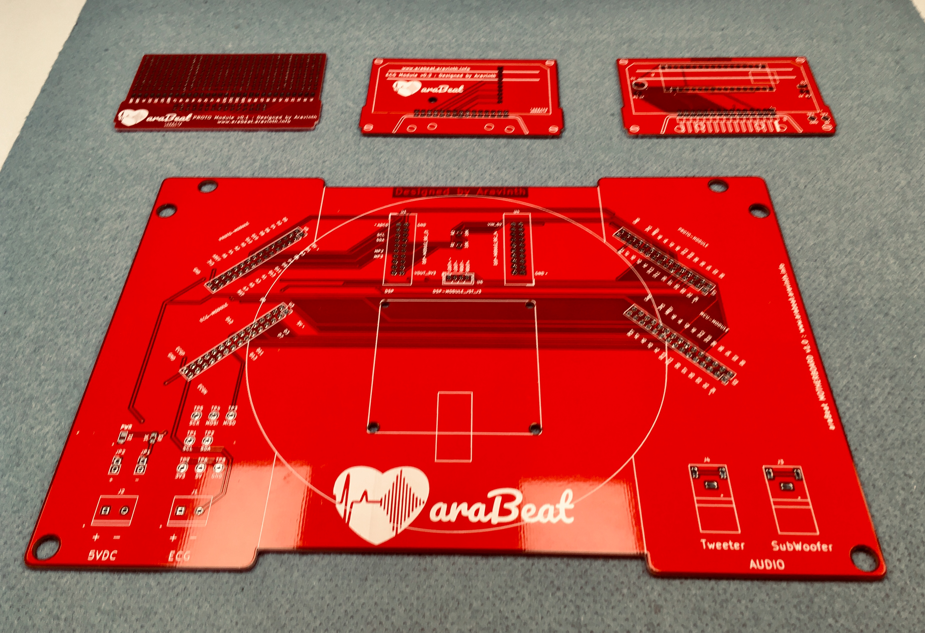
images/pcbs/arabeat-v1.0-3.jpg
