AravinthPanch/araBeat/images/pcbs/arabeat-v1.0-4.jpg

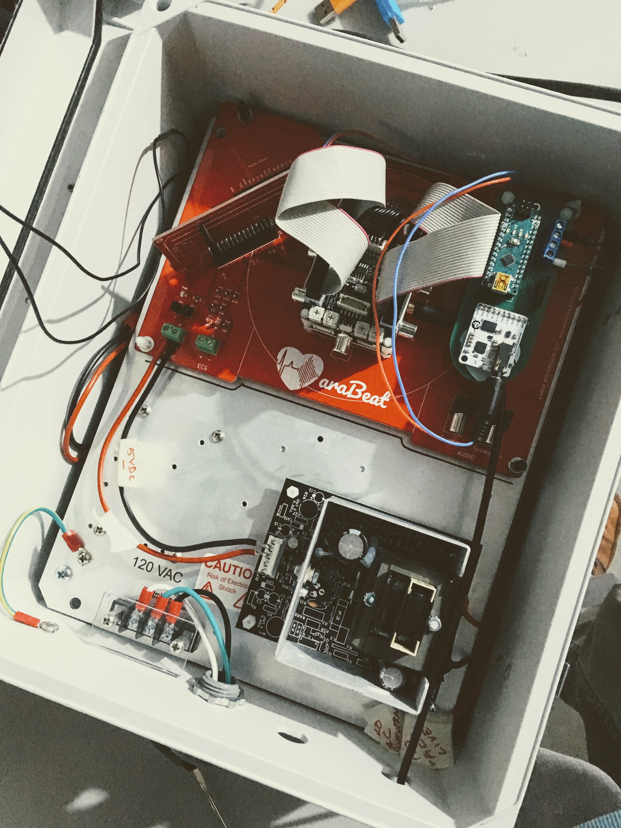
images/pcbs/arabeat-v1.0-4.jpg
