AravinthPanch/araBeat/images/sensor-frontend/design/design-2.jpg

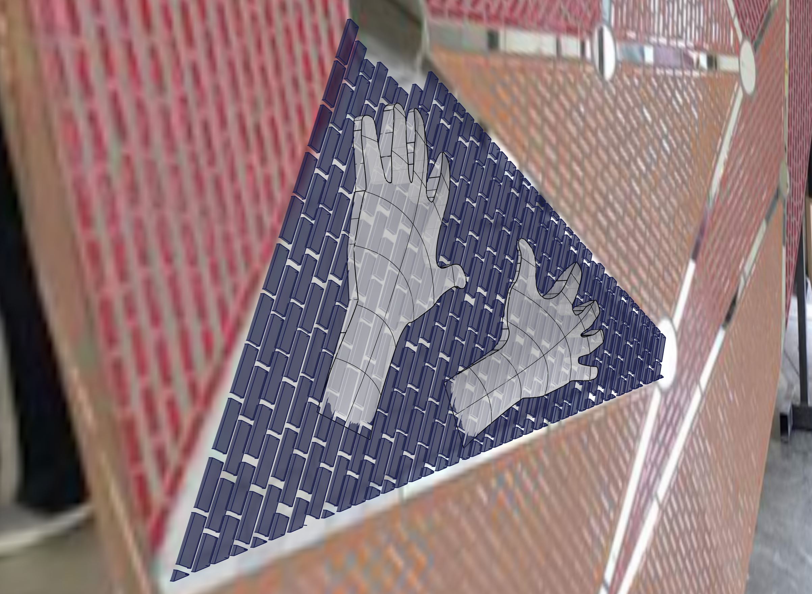
images/sensor-frontend/design/design-2.jpg
