AravinthPanch/araBeat/images/sensor-frontend/design/design-3.jpg

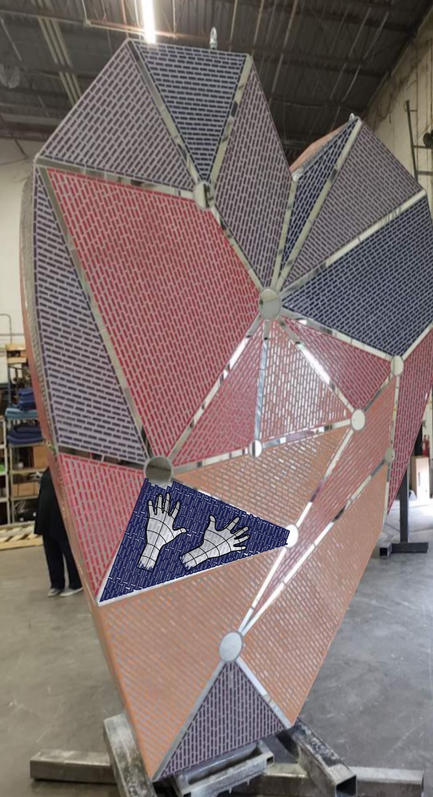
images/sensor-frontend/design/design-3.jpg
