AravinthPanch/araBeat/images/sensor-frontend/design/rhino-hands-1.jpg

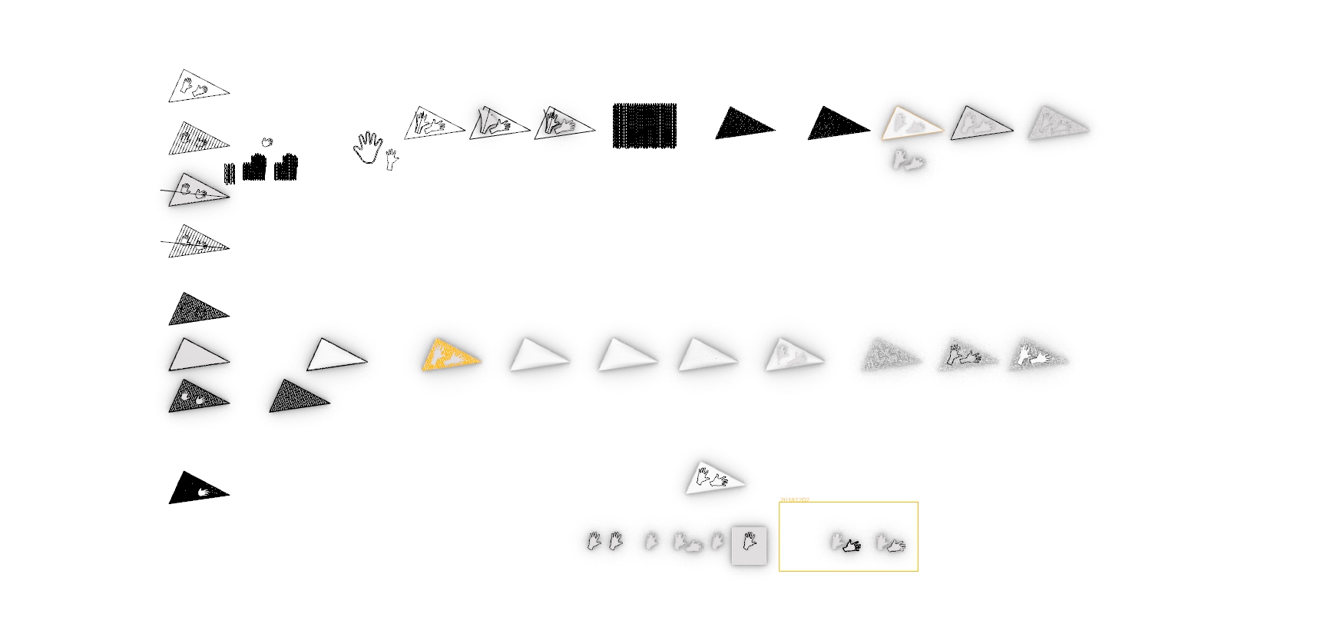
images/sensor-frontend/design/rhino-hands-1.jpg
