AravinthPanch/araBeat/images/sensor-frontend/design/rhino-hands-3.jpg

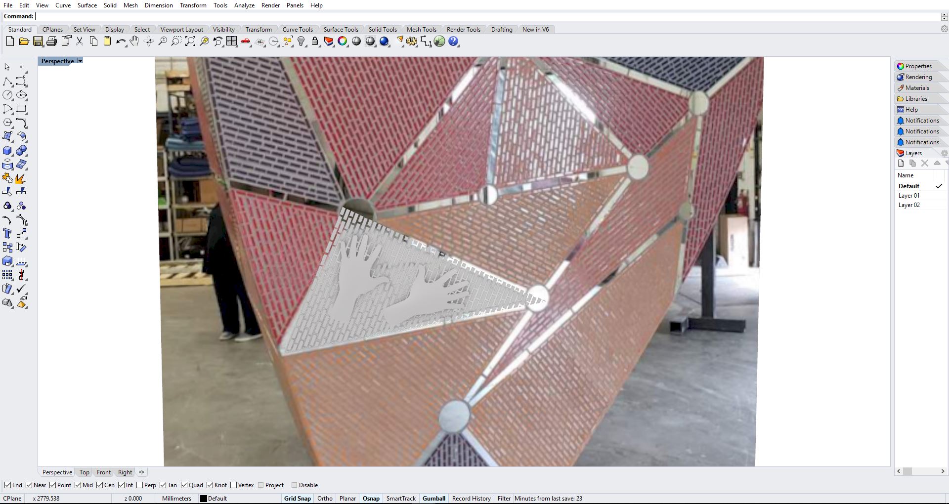
images/sensor-frontend/design/rhino-hands-3.jpg
