AravinthPanch/araBeat/images/sensor-frontend/prototype/foam-milling-3.jpg

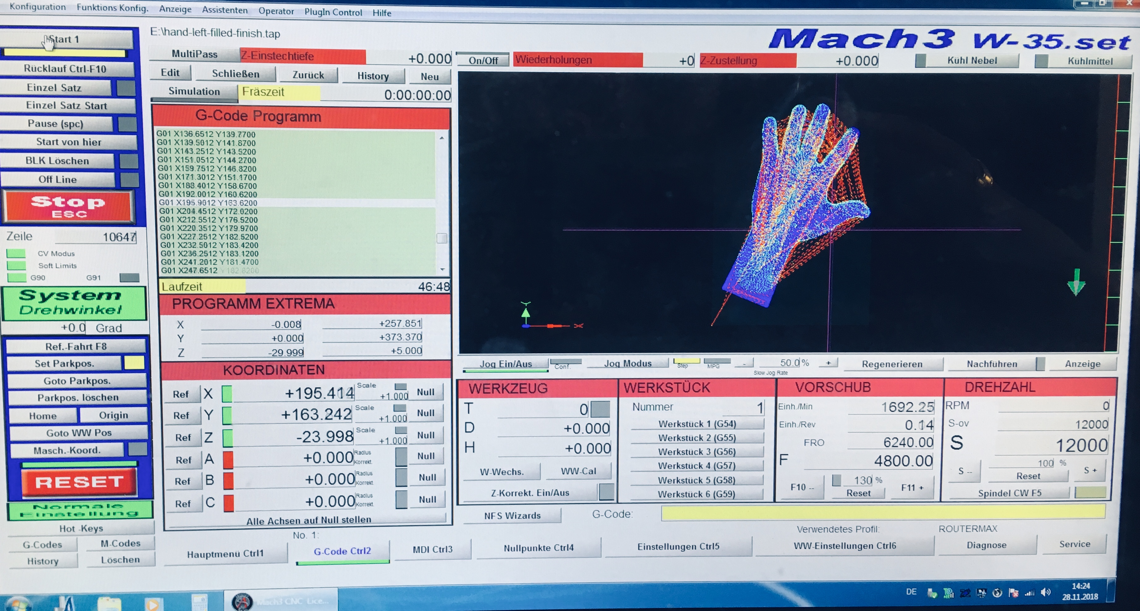
images/sensor-frontend/prototype/foam-milling-3.jpg
