AravinthPanch/araBeat/images/sensor-frontend/prototype/foam-milling-4.jpg

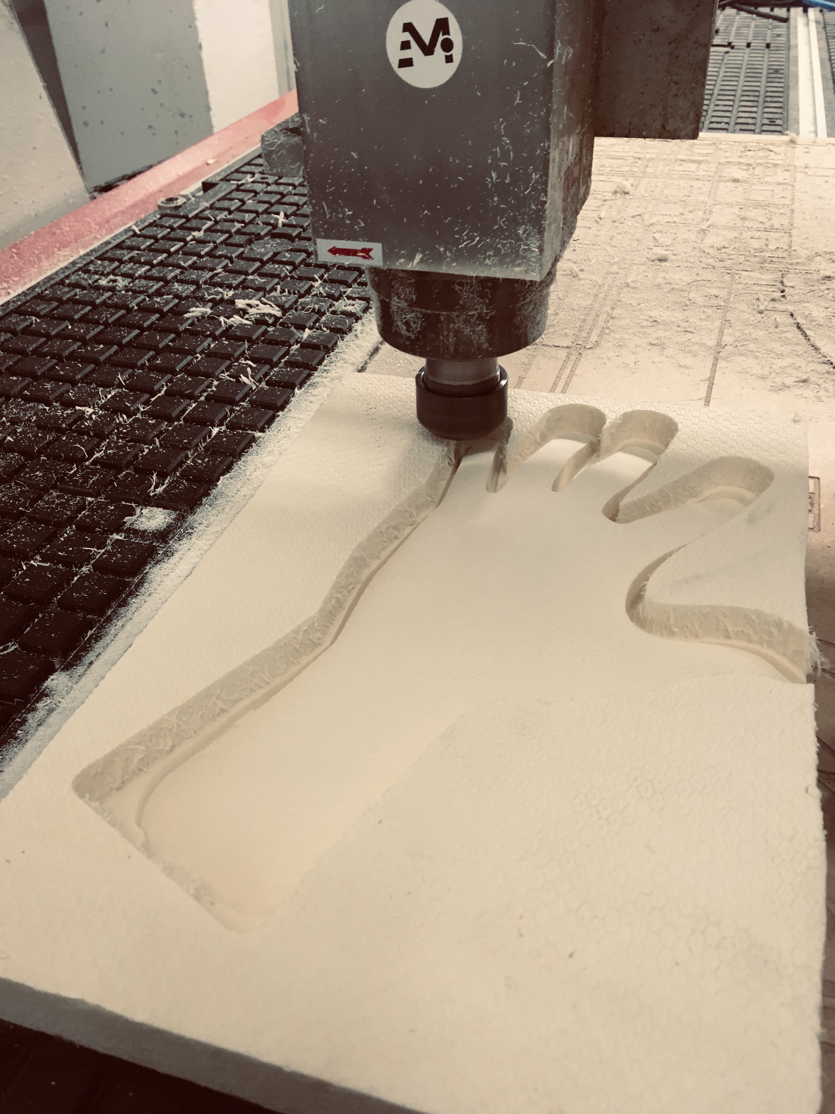
images/sensor-frontend/prototype/foam-milling-4.jpg
