AravinthPanch/araBeat/images/sensor-frontend/prototype/foam-milling-6.jpg

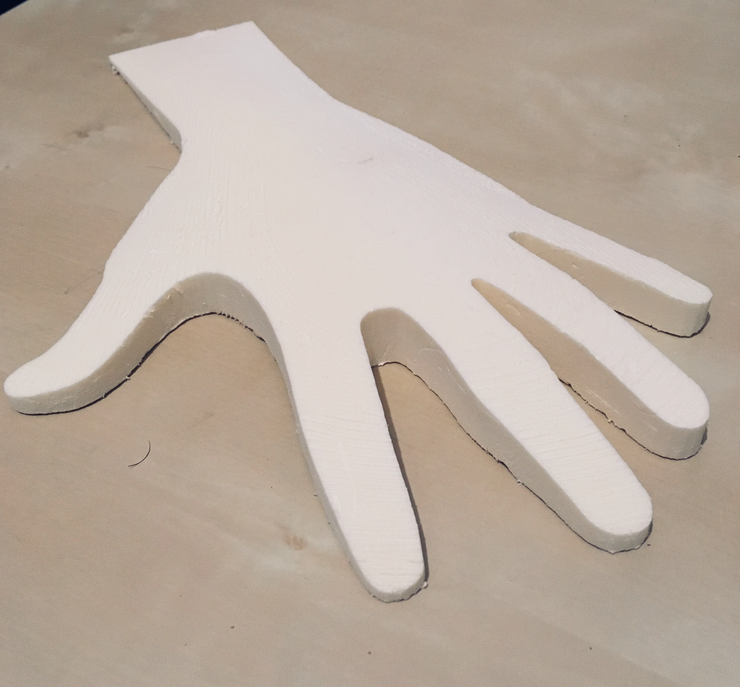
images/sensor-frontend/prototype/foam-milling-6.jpg
