AravinthPanch/araBeat/images/sensor-frontend/sensor-frontend-1.jpg

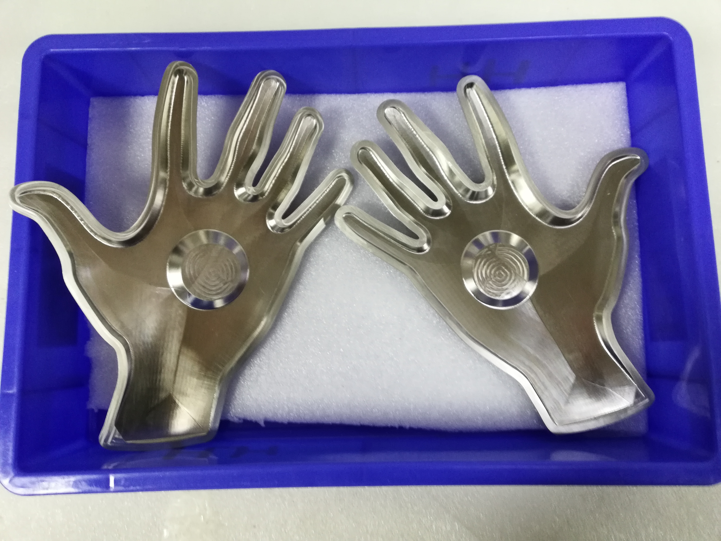
images/sensor-frontend/sensor-frontend-1.jpg
