AravinthPanch/araBeat/images/sensor-frontend/sensor-frontend-3.jpg

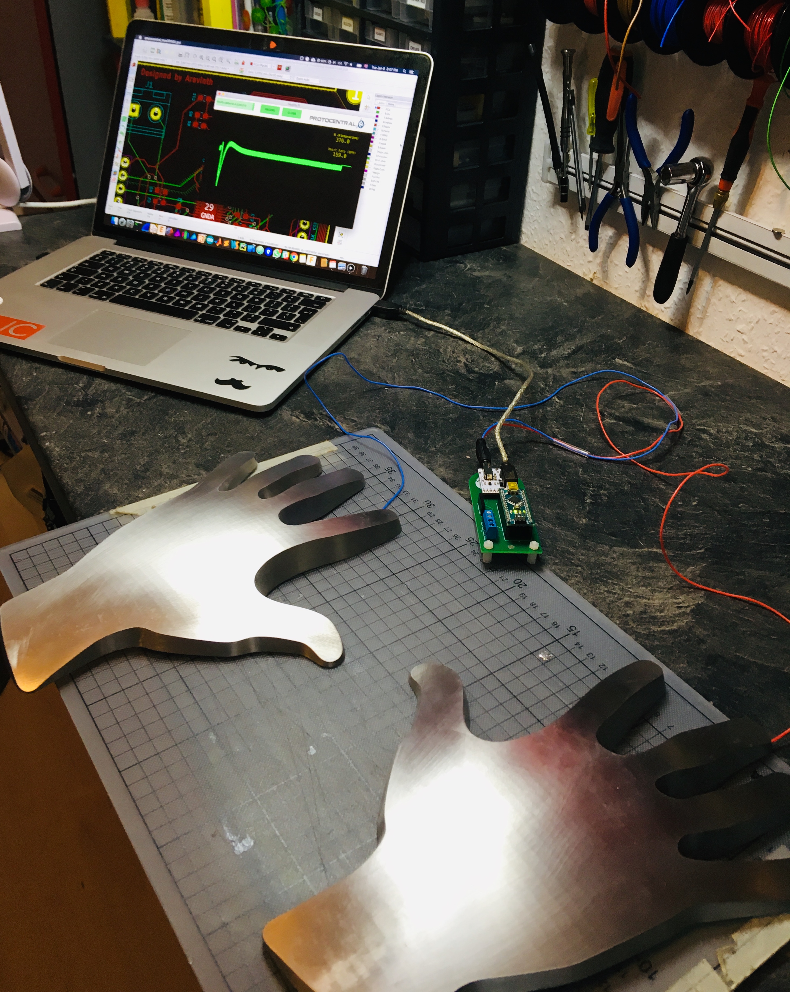
images/sensor-frontend/sensor-frontend-3.jpg
