AravinthPanch/araBeat/images/sensor-frontend/sensor-frontend-4.jpg

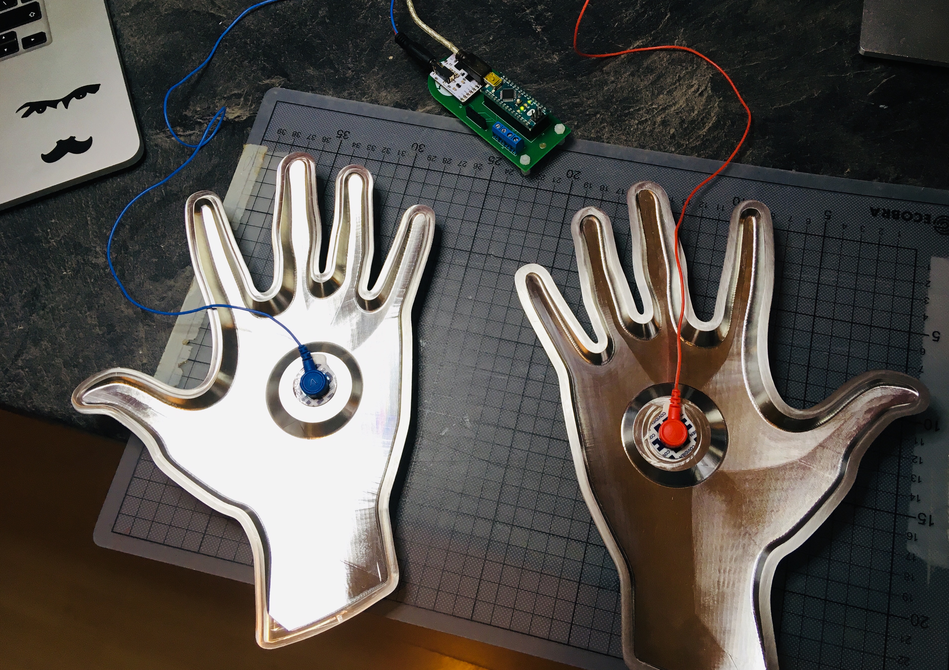
images/sensor-frontend/sensor-frontend-4.jpg
