AravinthPanch/araBeat/images/visits/ara+marc.jpeg

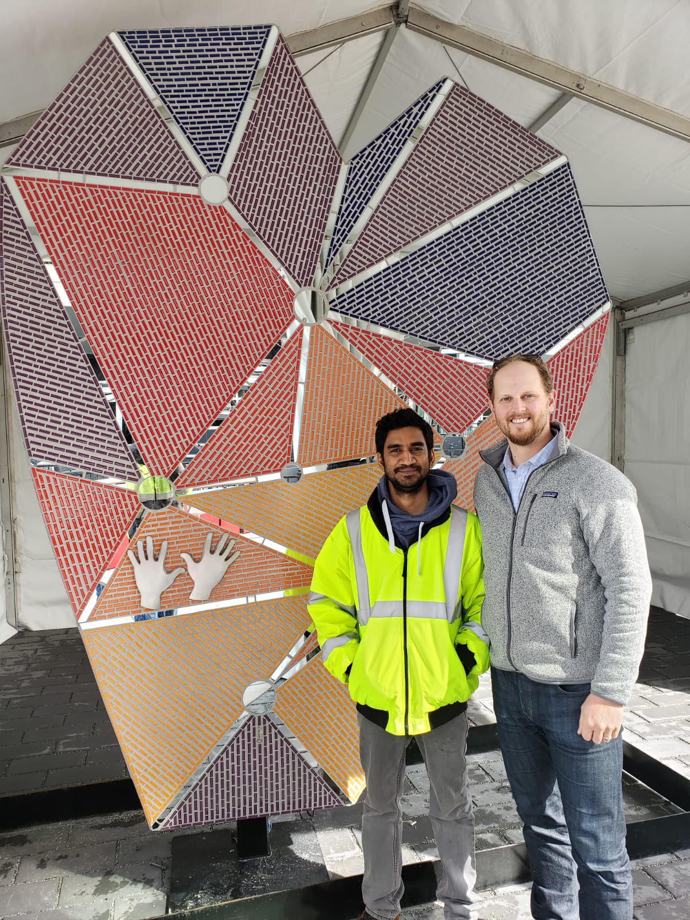
images/visits/ara+marc.jpeg
