AravinthPanch/araBeat/images/visits/ara+stacia.jpg

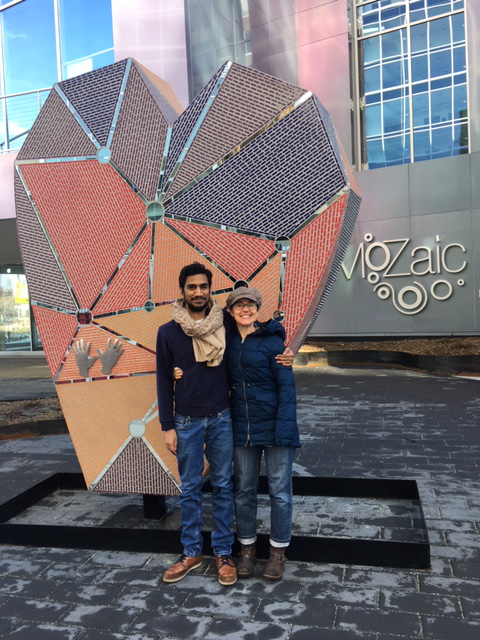
images/visits/ara+stacia.jpg
