AravinthPanch/araBeat/images/visits/stacia-1.jpg

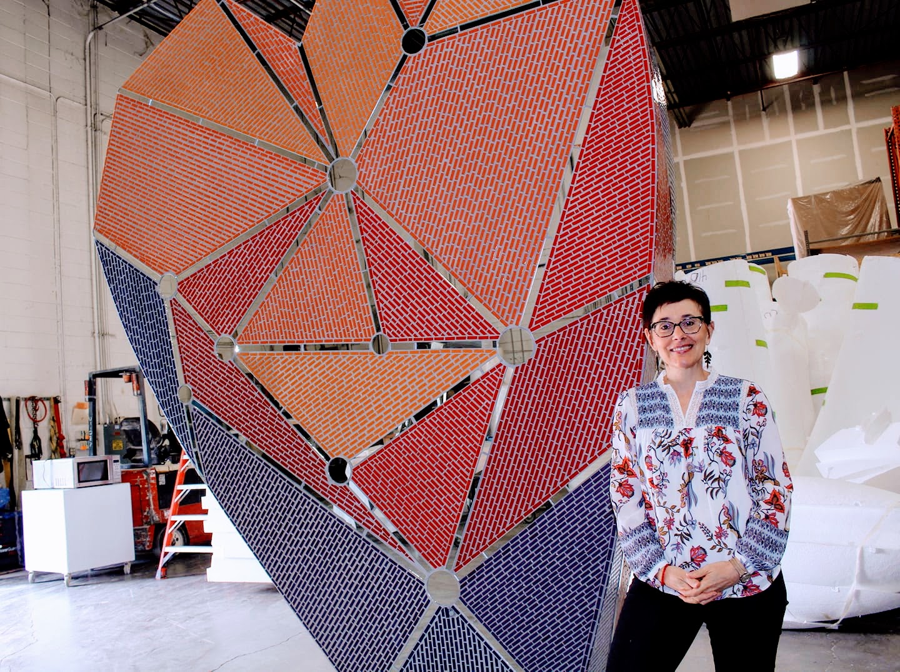
images/visits/stacia-1.jpg
