AravinthPanch/araBeat/images/visits/stacia-2.jpg

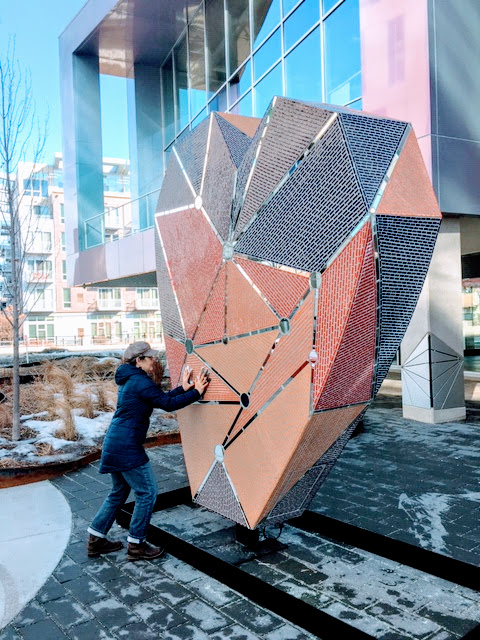
images/visits/stacia-2.jpg
