AravinthPanch/araBeat/images/visits/stuart-len-stacia.png

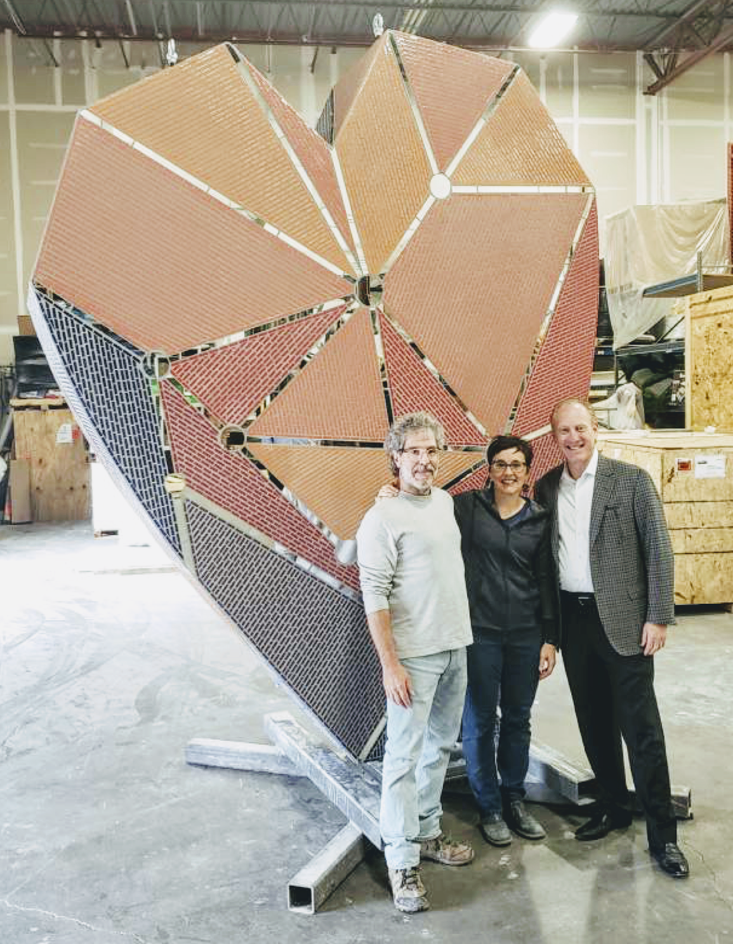
images/visits/stuart-len-stacia.png
