AravinthPanch/araBeat/software/arabeat_gui_osx.app/Contents/Java/data/fullscreen.png

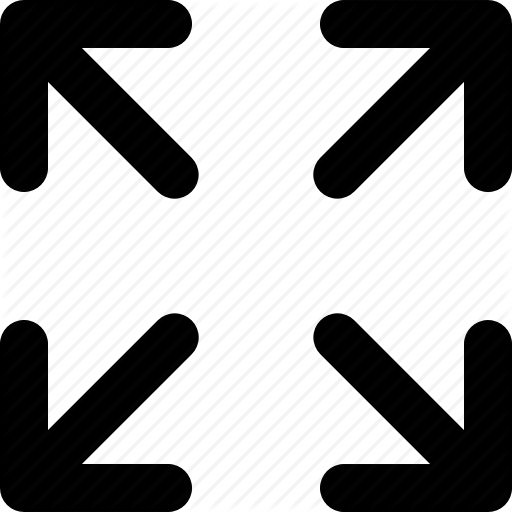
software/arabeat_gui_osx.app/Contents/Java/data/fullscreen.png
