AravinthPanch/araBeat/software/arabeat_gui_osx.app/Contents/Java/data/heart1.gif

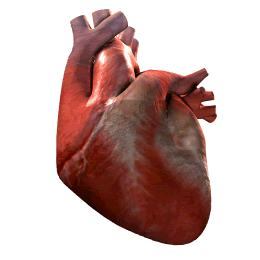
software/arabeat_gui_osx.app/Contents/Java/data/heart1.gif
