AravinthPanch/araBeat/software/arabeat_gui_osx.app/Contents/Java/data/minimize.png

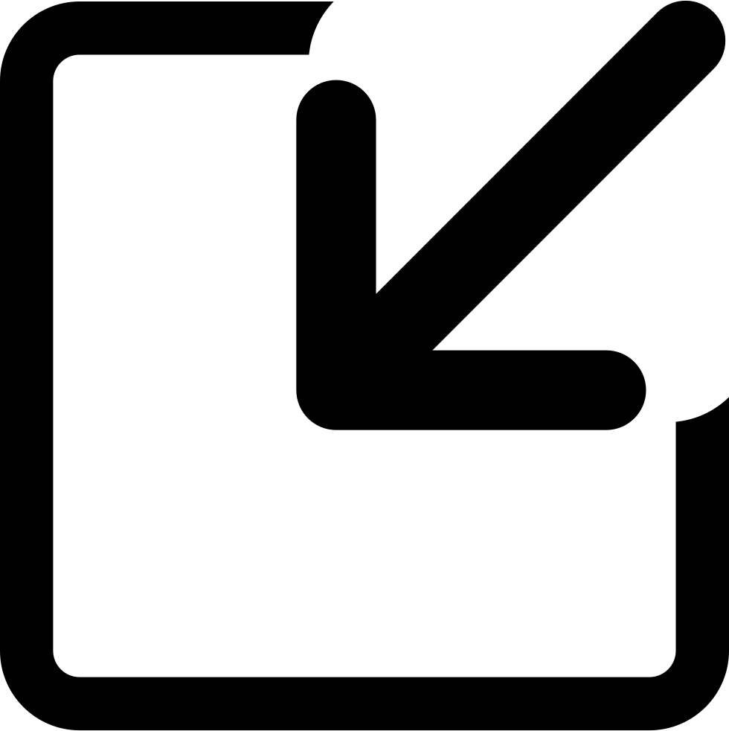
software/arabeat_gui_osx.app/Contents/Java/data/minimize.png
