AravinthPanch/araBeat/design/prototypes/mini-speaker-enclosure/enclosure-front.stl

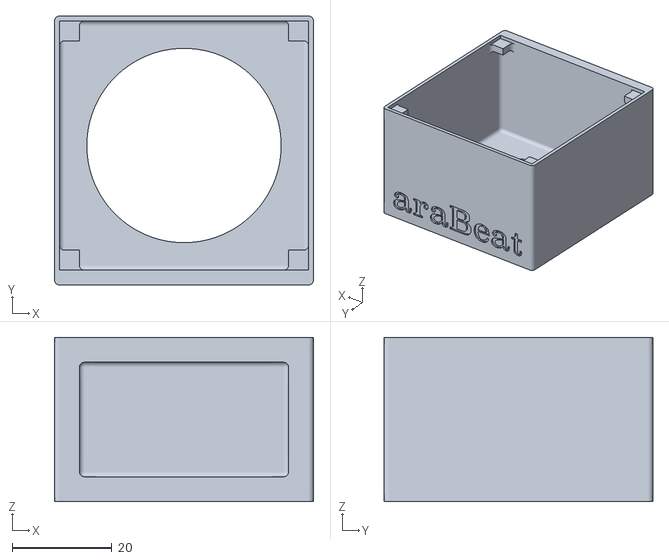
[picture p171: CAD file, 2018-07-11]
design/prototypes/mini-speaker-enclosure/enclosure-front.stl
52.0 x 54.0 x 33.0
