AravinthPanch/araBeat/design/sensor-frontend/design-1-long/left-filled.stl

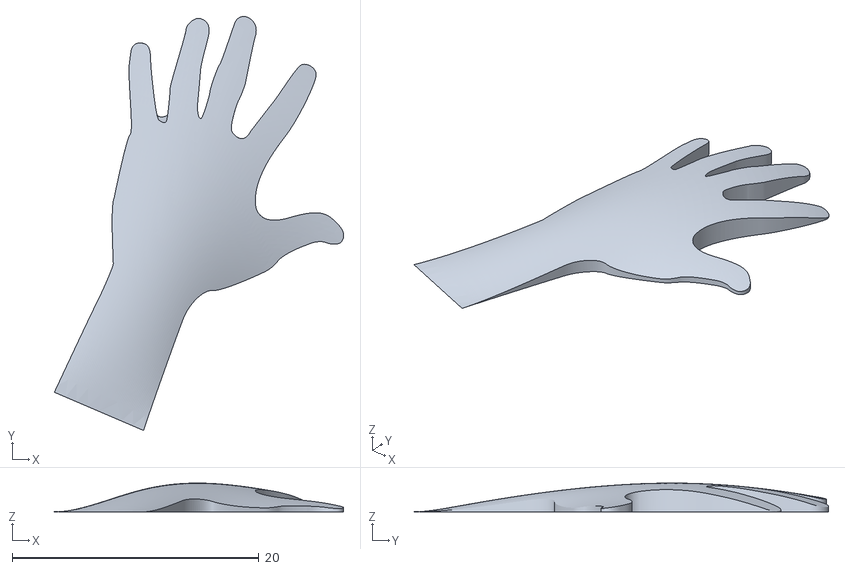
[picture p172: CAD file, 2018-12-22]
design/sensor-frontend/design-1-long/left-filled.stl
23.4 x 33.5 x 2.33
