AravinthPanch/araBeat/hardware/-resources/3d-models/keystone-5000.step

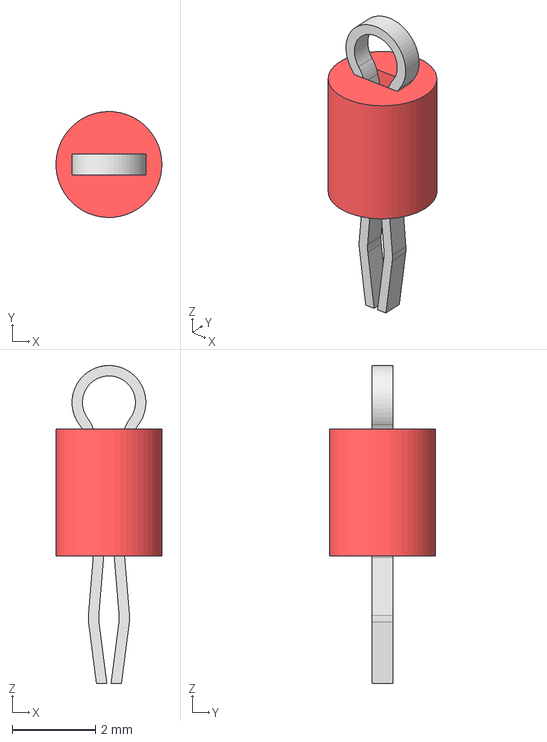
[picture p173: CAD file, 2019-03-02]
hardware/-resources/3d-models/keystone-5000.step
2.54 x 2.54 x 7.62 mm
