AravinthPanch/araBeat/hardware/-resources/edgecut-silkscreen/ecg-baseboard-edgecut.dxf

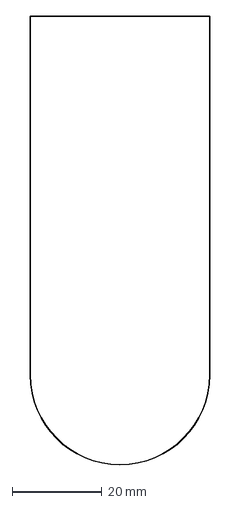
[picture p174: CAD file, 2018-11-09]
hardware/-resources/edgecut-silkscreen/ecg-baseboard-edgecut.dxf
40.0 x 100.0 mm
