AravinthPanch/araBeat/hardware/-resources/edgecut-silkscreen/ecg-cassette/ecg-cassette-mark.dxf

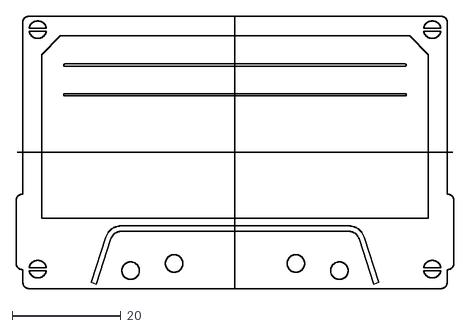
[picture p175: CAD file, 2019-02-02]
hardware/-resources/edgecut-silkscreen/ecg-cassette/ecg-cassette-mark.dxf
80.4 x 50.0
