AravinthPanch/araBeat/hardware/-resources/edgecut-silkscreen/ecg-module/ecg-module-marker.dxf

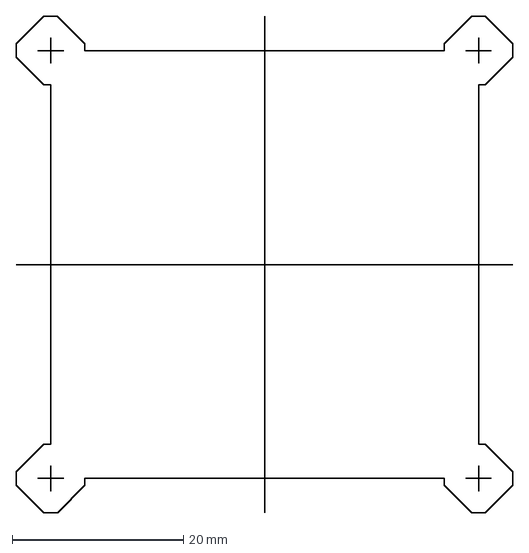
[picture p176: CAD file, 2018-11-17]
hardware/-resources/edgecut-silkscreen/ecg-module/ecg-module-marker.dxf
58.0 x 58.0 mm
