AravinthPanch/araBeat/hardware/-resources/edgecut-silkscreen/heated-plate/heated-plate-outline.dxf

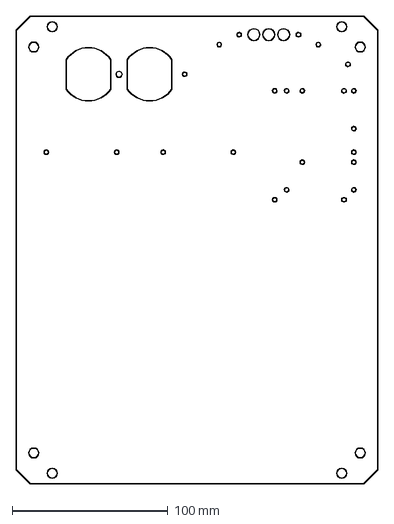
[picture p177: CAD file, 2019-01-30]
hardware/-resources/edgecut-silkscreen/heated-plate/heated-plate-outline.dxf
231.8 x 300.0 mm
