AravinthPanch/araBeat/hardware/-resources/edgecut-silkscreen/motherboard/motherboard-edgecut.dxf

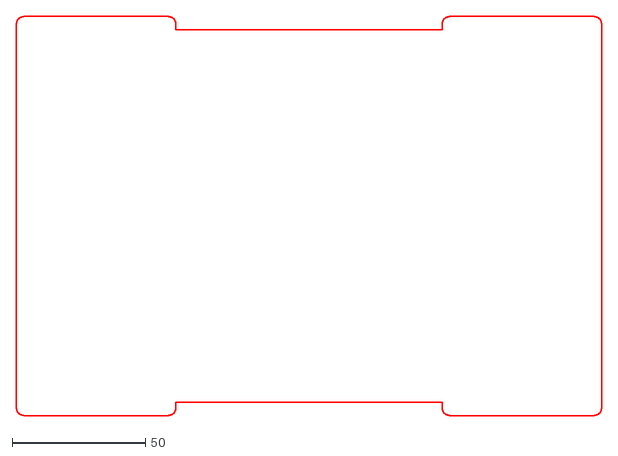
[picture p178: CAD file, 2019-02-26]
hardware/-resources/edgecut-silkscreen/motherboard/motherboard-edgecut.dxf
220.0 x 150.0
