AravinthPanch/araBeat/design/audio-rack/tweeter-disc.dxf

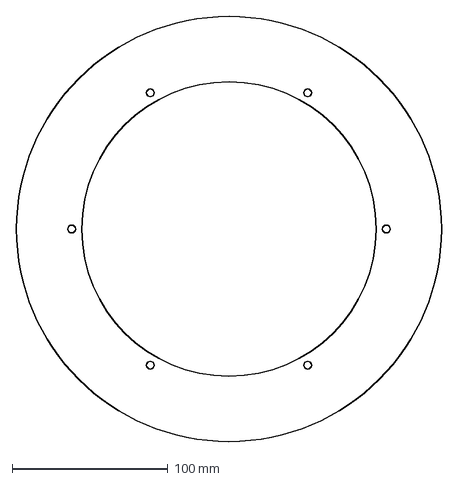
[picture p179: CAD file, 2019-02-12]
design/audio-rack/tweeter-disc.dxf
273.0 x 273.0 mm
