AravinthPanch/araBeat/design/sensor-frontend/design-1-long/right-shell.stl

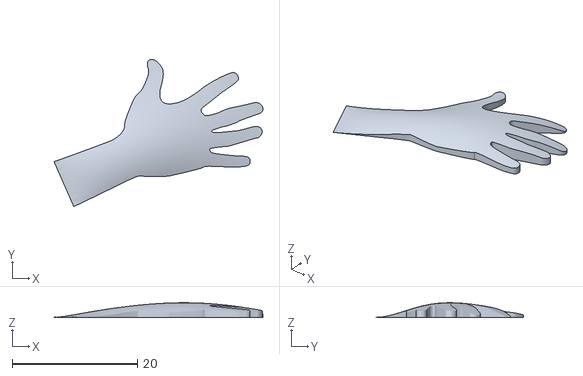
[picture p180: CAD file, 2018-11-29]
design/sensor-frontend/design-1-long/right-shell.stl
33.4 x 23.6 x 2.33
