AravinthPanch/araBeat/design/sensor-frontend/design-2-chamfer/left-right-chamfer.stp

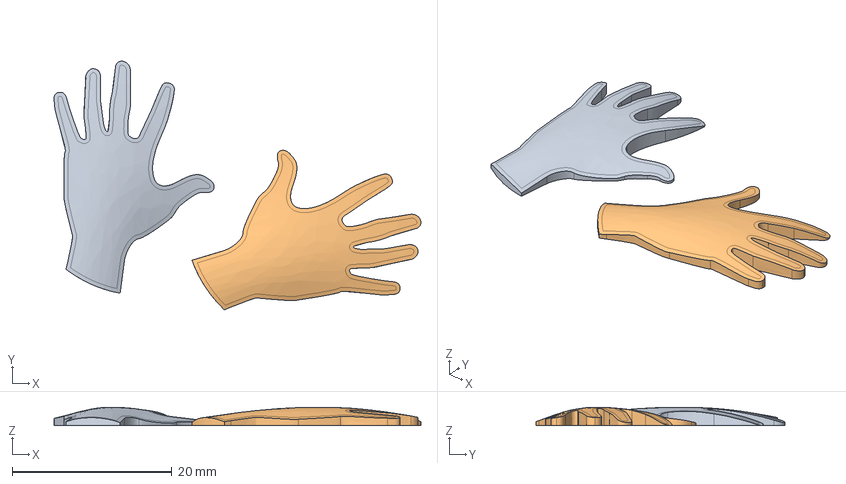
[picture p181: CAD file, 2018-12-22]
design/sensor-frontend/design-2-chamfer/left-right-chamfer.stp
46.0 x 31.2 x 2.32 mm
