AravinthPanch/araBeat/design/sensor-frontend/design-3-no-chamfer/left-right-no-chamfer.stp

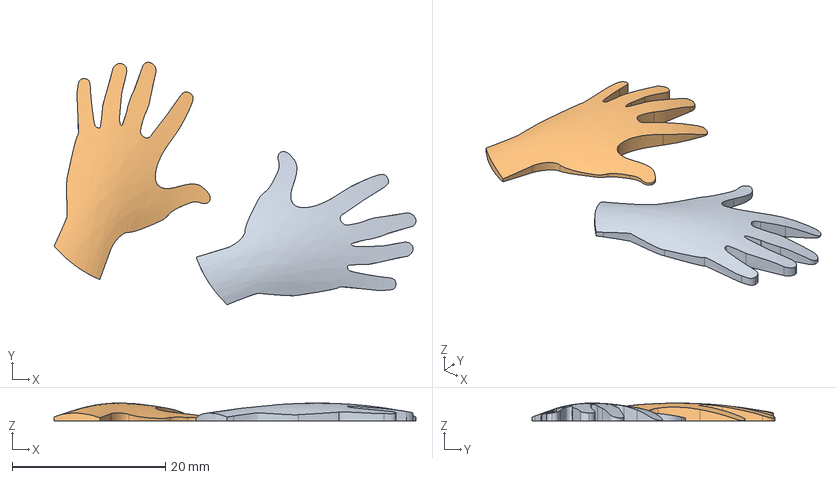
[picture p182: CAD file, 2018-12-22]
design/sensor-frontend/design-3-no-chamfer/left-right-no-chamfer.stp
47.2 x 31.7 x 2.32 mm
