AravinthPanch/araBeat/hardware/-resources/3d-models/mcu-cassette.step

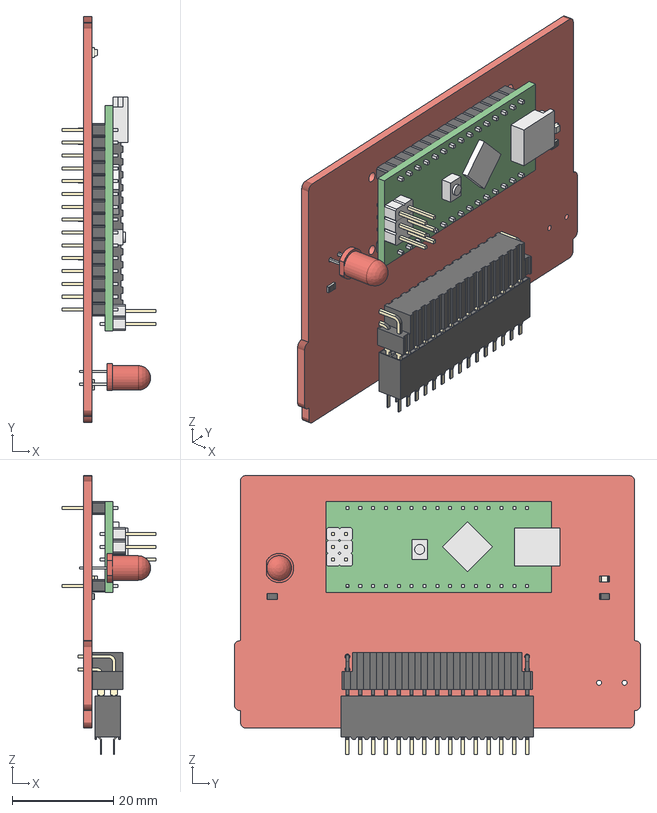
[picture p183: CAD file, 2019-02-26]
hardware/-resources/3d-models/mcu-cassette.step
18.5 x 80.4 x 55.2 mm
