AravinthPanch/araBeat/hardware/-resources/edgecut-silkscreen/ecg-cassette/ecg-cassette-edgecut.dxf

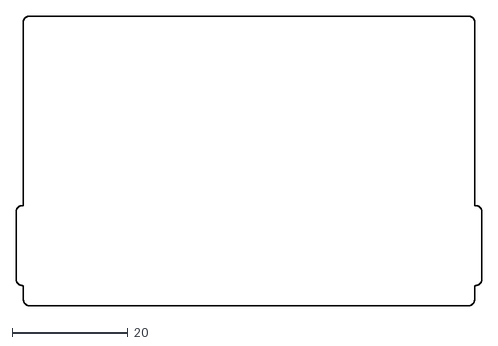
[picture p184: CAD file, 2019-02-02]
hardware/-resources/edgecut-silkscreen/ecg-cassette/ecg-cassette-edgecut.dxf
80.4 x 50.0
