AravinthPanch/araBeat/hardware/-resources/edgecut-silkscreen/motherboard/motherboard-silkscreen.dxf

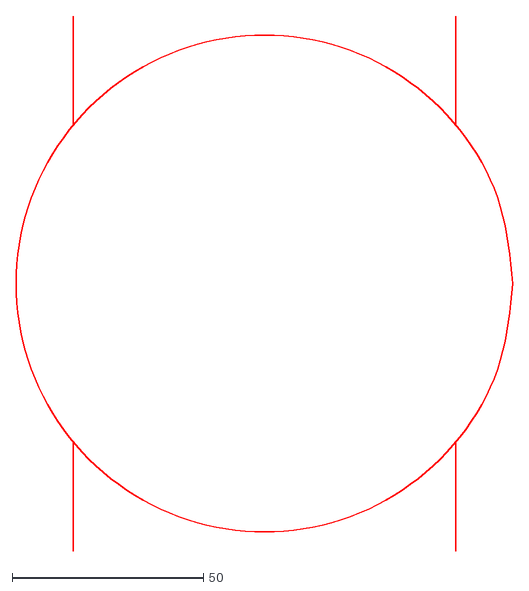
[picture p185: CAD file, 2019-02-26]
hardware/-resources/edgecut-silkscreen/motherboard/motherboard-silkscreen.dxf
130.0 x 140.0
