AravinthPanch/araBeat/design/sensor-frontend/design-1-long/left-right-mosaic.stp

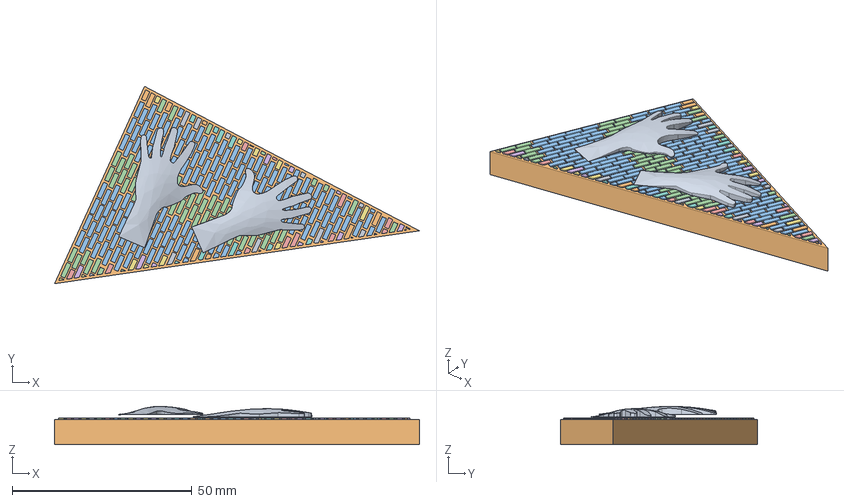
[picture p186: CAD file, 2018-11-29]
design/sensor-frontend/design-1-long/left-right-mosaic.stp
101.7 x 55.0 x 10.7 mm
