AravinthPanch/araBeat/hardware/-resources/3d-models/proto-module.step

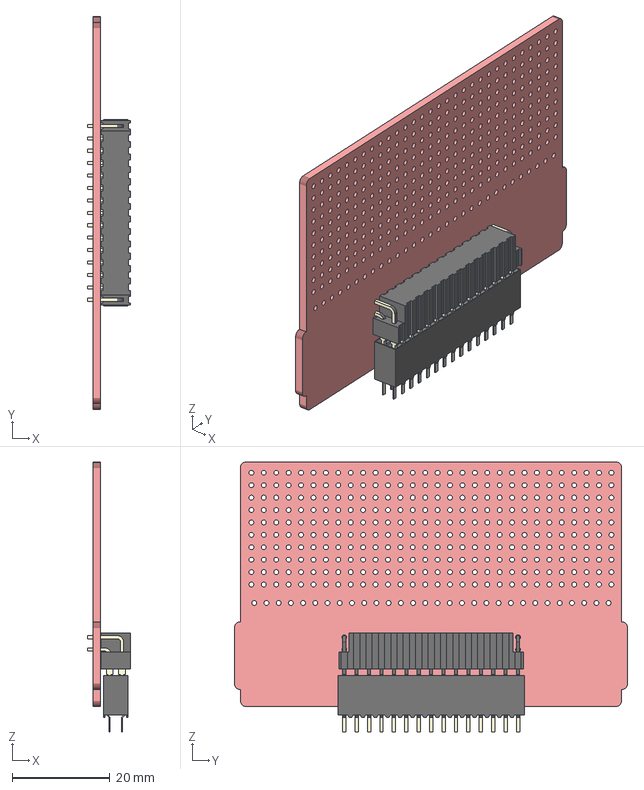
[picture p187: CAD file, 2019-02-26]
hardware/-resources/3d-models/proto-module.step
8.84 x 80.4 x 55.2 mm
