AravinthPanch/araBeat/hardware/-resources/edgecut-silkscreen/motherboard/motherboard-mark.dxf

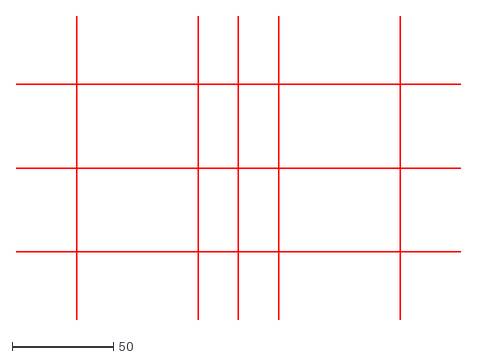
[picture p188: CAD file, 2019-02-26]
hardware/-resources/edgecut-silkscreen/motherboard/motherboard-mark.dxf
220.0 x 150.0
