AravinthPanch/araBeat/hardware/-resources/3d-models/ecg-cassette.step

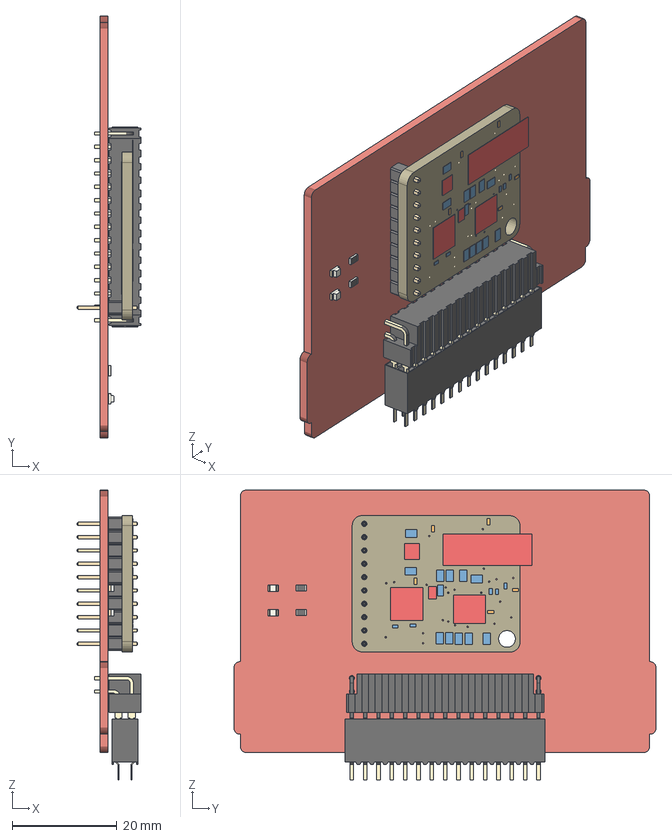
[picture p189: CAD file, 2019-02-26]
hardware/-resources/3d-models/ecg-cassette.step
12.2 x 80.4 x 55.2 mm
