AravinthPanch/araBeat/hardware/-resources/3d-models/ecg-baseboard.step

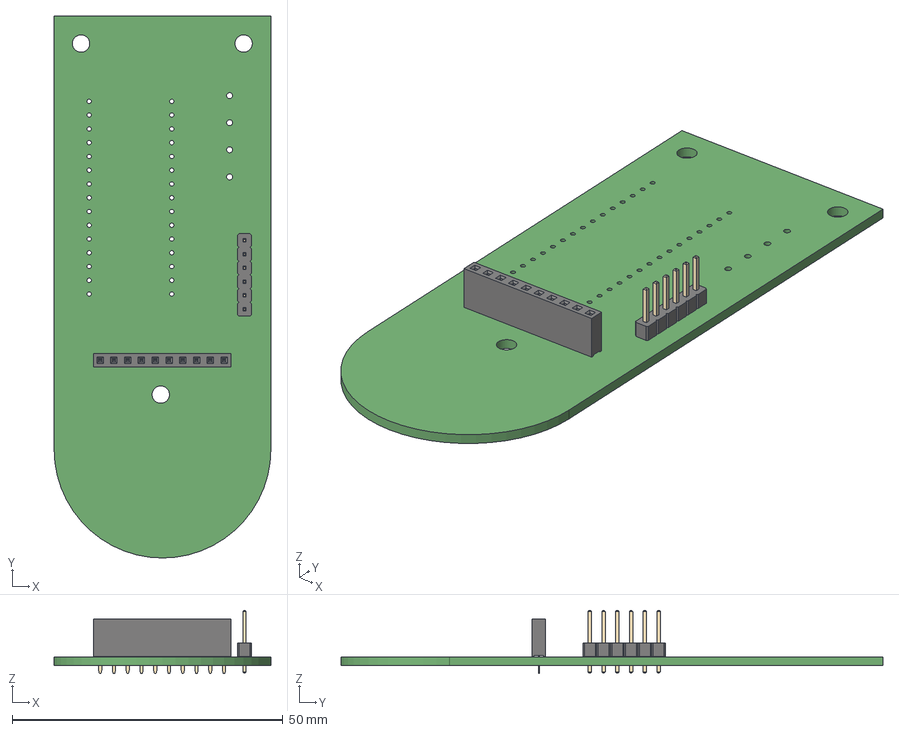
[picture p190: CAD file, 2018-11-10]
hardware/-resources/3d-models/ecg-baseboard.step
40.0 x 100.0 x 11.6 mm
