AravinthPanch/araBeat/docs/ecg/wiring.jpg

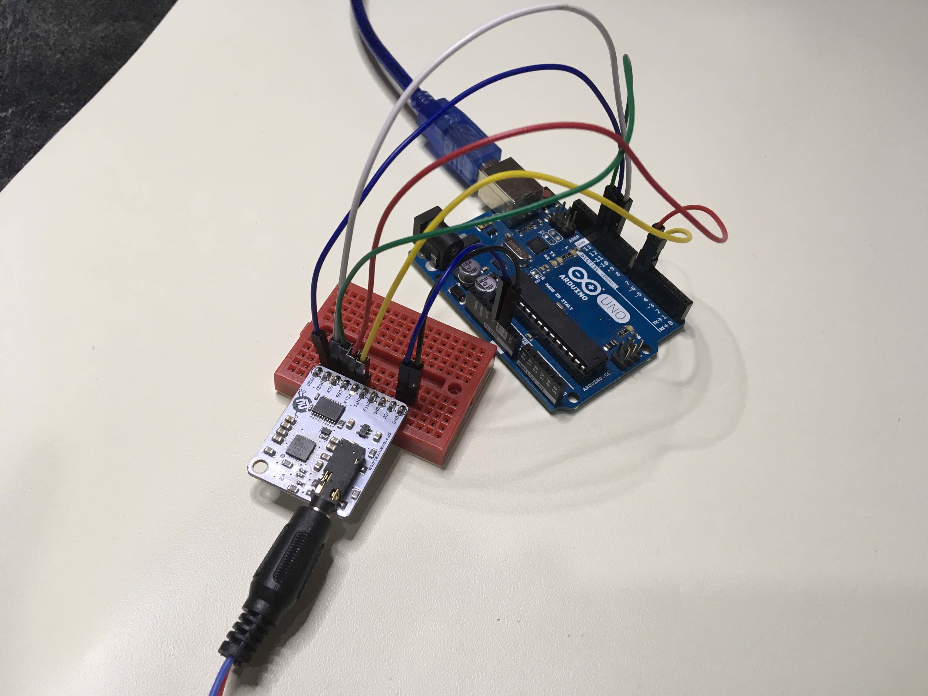
docs/ecg/wiring.jpg
