AravinthPanch/araBeat/images/behind-the-scenes/ara-soldering.jpg

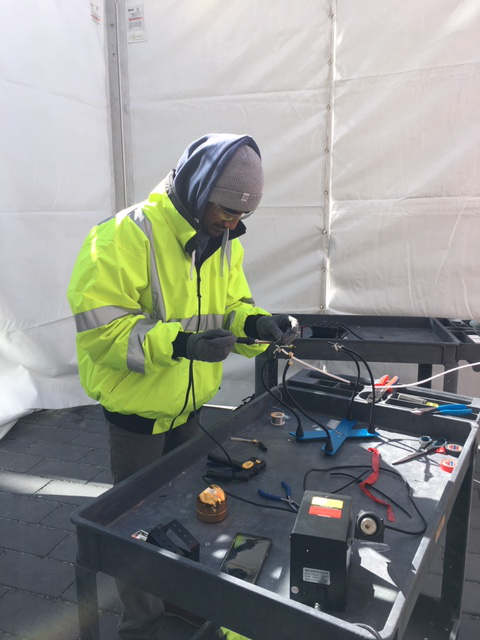
images/behind-the-scenes/ara-soldering.jpg
