AravinthPanch/araBeat/images/installation/installation-5.jpg

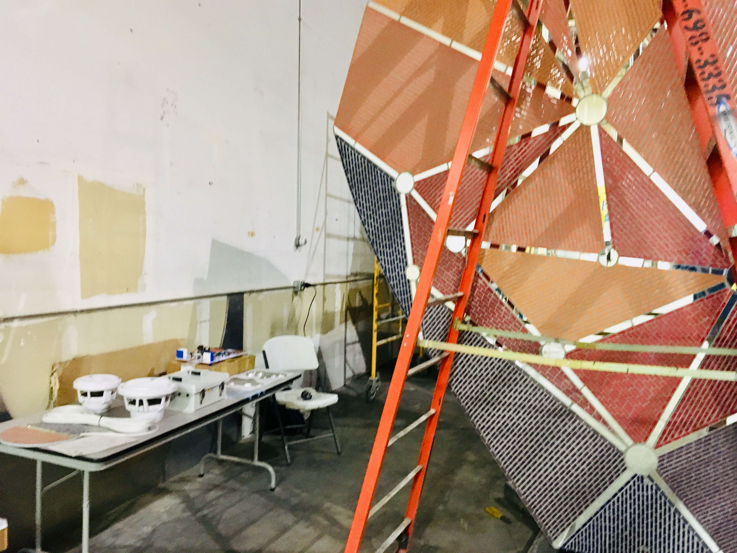
images/installation/installation-5.jpg
