AravinthPanch/araBeat/images/behind-the-scenes/ara-arabeat-tuning.jpg

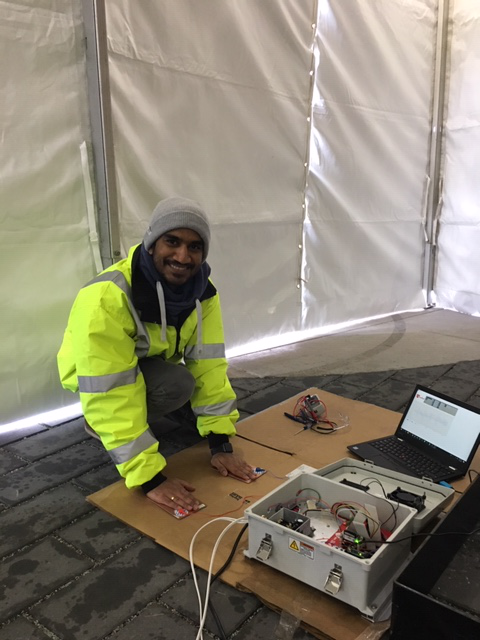
images/behind-the-scenes/ara-arabeat-tuning.jpg
