AravinthPanch/araBeat/research/audio/bumpy-mp3/bumpy-pcb/test.png

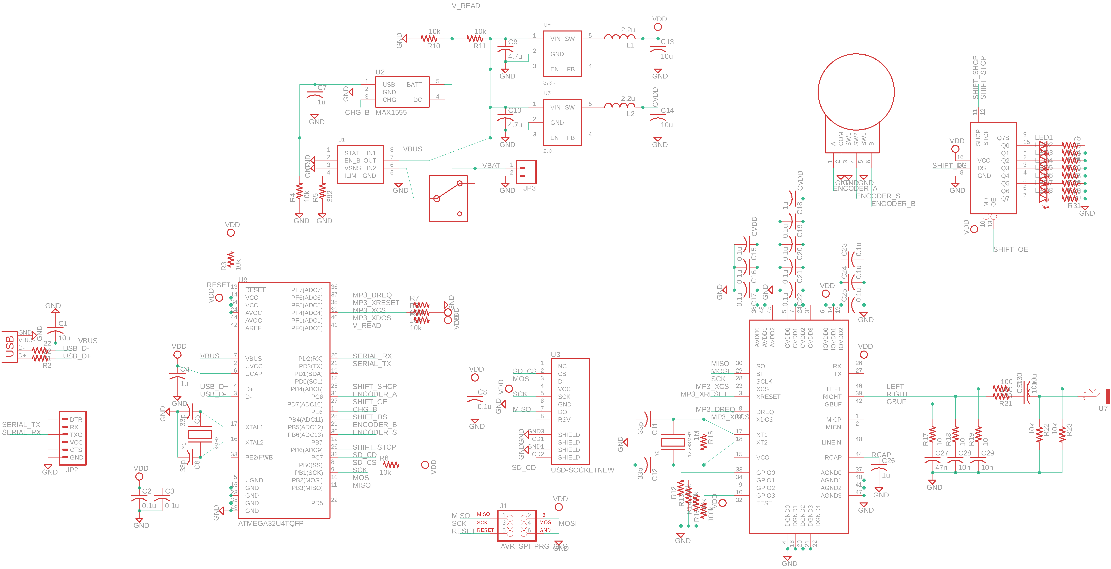
research/audio/bumpy-mp3/bumpy-pcb/test.png
