AravinthPanch/araBeat/hardware/-resources/reference-designs/pc_max30003.pdf

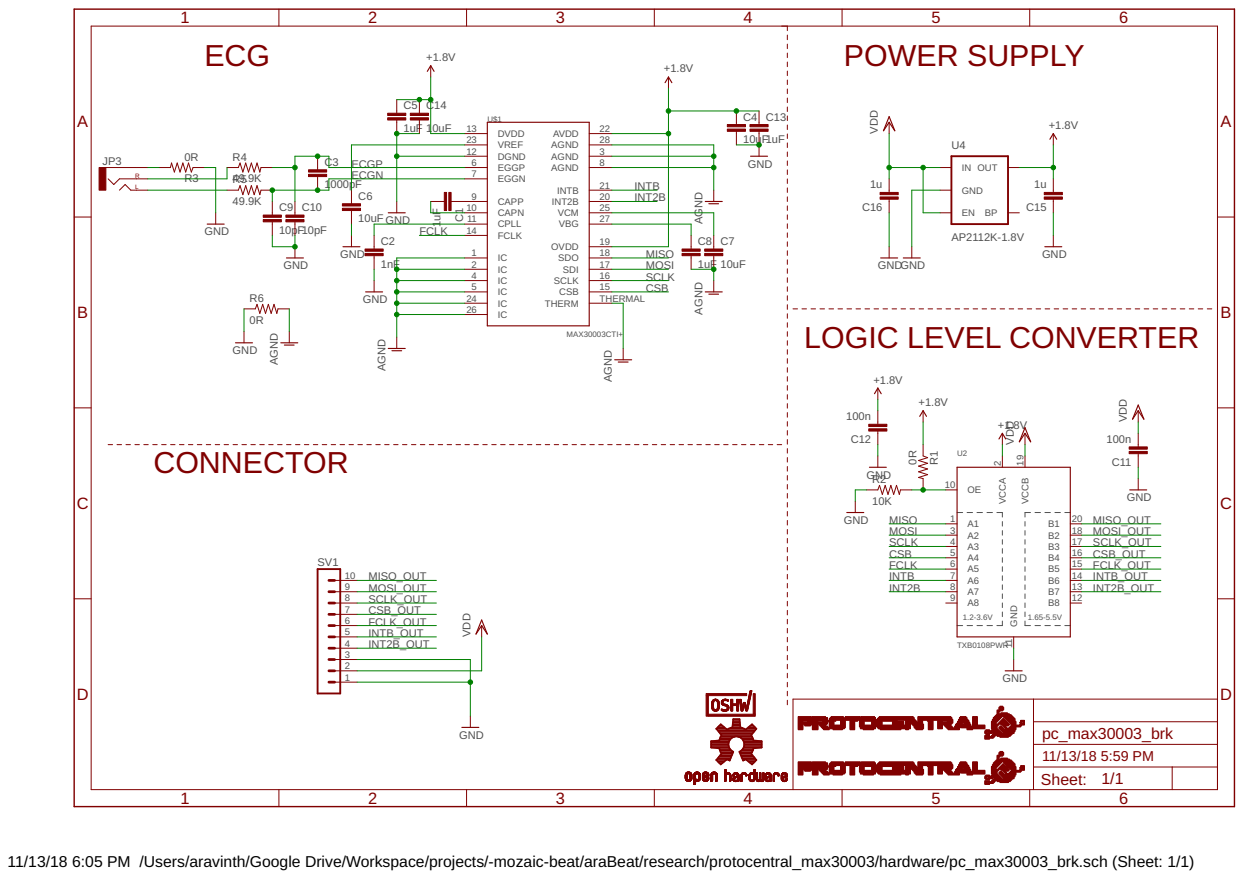
[picture p210: page 1]

2 | 16 SDI 17 SDO MOSI
4 | SCLK
5 | 15 SCLK CSB
24 | THERMAL

11/13/18 6:05 PM /Users/aravinth/Google Drive/Workspace/projects/-mozaic-beat/araBeat/research/protocentral_max30003/hardware/pc_max30003_brk.sch (Sheet: 1/1)
