AravinthPanch/araBeat/research/ecg/dfrobot-ecg/schematic.pdf

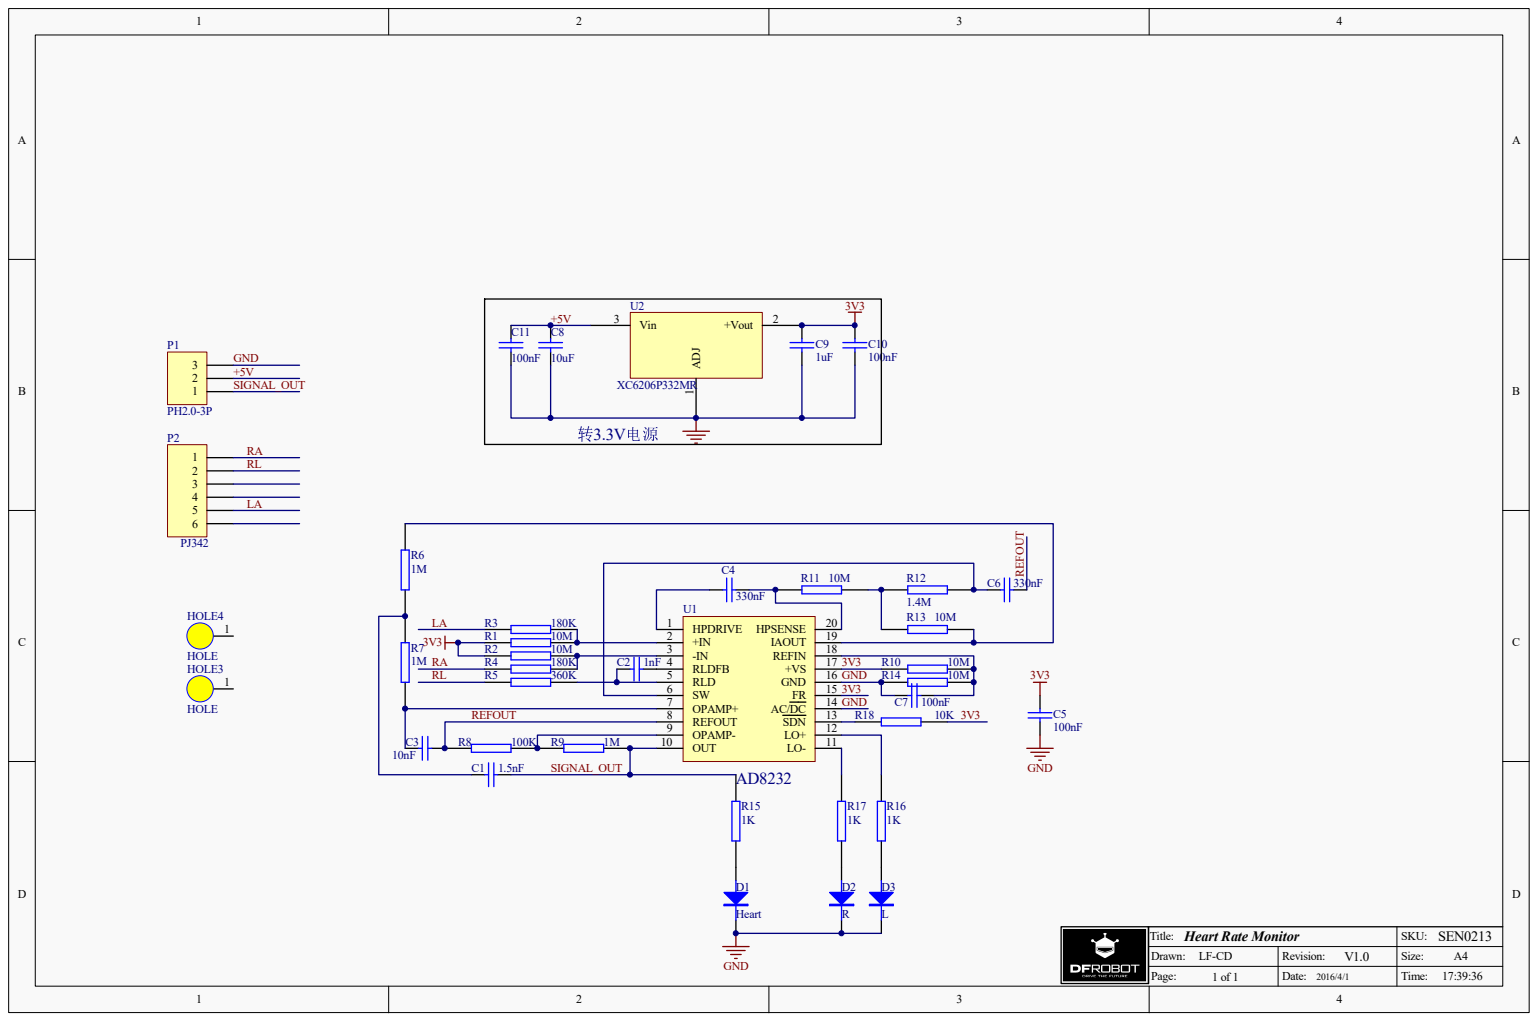
[picture p211: page 1]
