AravinthPanch/araBeat/research/audio/music-maker-midi/src/VS1053.h

/**
   Author: Aravinth Panchadcharam
   Email: me@aravinth.info
   Date: 11/07/18.
   Project: araBeat
*/

#define VS1053_RX  2 // This is the pin that connects to the RX pin on VS1053
#define VS1053_RESET 9 // This is the pin that connects to the RESET pin on VS1053

// See http://www.vlsi.fi/fileadmin/datasheets/vs1053.pdf Pg 31
#define VS1053_BANK_DEFAULT 0x00
#define VS1053_BANK_DRUMS1 0x78
#define VS1053_BANK_DRUMS2 0x7F
#define VS1053_BANK_MELODY 0x79

// See http://www.vlsi.fi/fileadmin/datasheets/vs1053.pdf Pg 32 for more!
#define VS1053_GM1_OCARINA 80

#define MIDI_NOTE_ON  0x90
#define MIDI_NOTE_OFF 0x80
#define MIDI_CHAN_MSG 0xB0
#define MIDI_CHAN_BANK 0x00
#define MIDI_CHAN_VOLUME 0x07
#define MIDI_CHAN_PROGRAM 0xC0
