AravinthPanch/araBeat/research/audio/music-maker-midi/src/midi.cpp

/**
   Author: Aravinth Panchadcharam
   Email: me@aravinth.info
   Date: 11/07/18.
   Project: araBeat
*/

#include "midi.h"

SoftwareSerial VS1053_MIDI(0, 2);

midi::midi(){
  VS1053_MIDI.begin(31250);
}

void midi::setInstrument(uint8_t chan, uint8_t inst) {
  if (chan > 15) return;
  inst --;
  if (inst > 127) return;

  VS1053_MIDI.write(MIDI_CHAN_PROGRAM | chan);
  VS1053_MIDI.write(inst);
}


void midi::setChannelVolume(uint8_t chan, uint8_t vol) {
  if (chan > 15) return;
  if (vol > 127) return;

  VS1053_MIDI.write(MIDI_CHAN_MSG | chan);
  VS1053_MIDI.write(MIDI_CHAN_VOLUME);
  VS1053_MIDI.write(vol);
}

void midi::setChannelBank(uint8_t chan, uint8_t bank) {
  if (chan > 15) return;
  if (bank > 127) return;

  VS1053_MIDI.write(MIDI_CHAN_MSG | chan);
  VS1053_MIDI.write((uint8_t)MIDI_CHAN_BANK);
  VS1053_MIDI.write(bank);
}

void midi::noteOn(uint8_t chan, uint8_t n, uint8_t vel) {
  if (chan > 15) return;
  if (n > 127) return;
  if (vel > 127) return;

  VS1053_MIDI.write(MIDI_NOTE_ON | chan);
  VS1053_MIDI.write(n);
  VS1053_MIDI.write(vel);
}

void midi::noteOff(uint8_t chan, uint8_t n, uint8_t vel) {
  if (chan > 15) return;
  if (n > 127) return;
  if (vel > 127) return;

  VS1053_MIDI.write(MIDI_NOTE_OFF | chan);
  VS1053_MIDI.write(n);
  VS1053_MIDI.write(vel);
}
