AravinthPanch/araBeat/firmware/dsp/test/i2c-beep/export/i2c-beep_IC_1.h

/*
 * File:           C:\Users\NBT\Desktop\araBeat\firmware\dsp\test\i2c-beep\export\i2c-beep_IC_1.h
 *
 * Created:        Wednesday, February 20, 2019 5:09:55 PM
 * Description:    i2c-beep:IC 1 program data.
 *
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
 * This software may only be used to program products purchased from
 * Analog Devices for incorporation by you into audio products that
 * are intended for resale to audio product end users. This software
 * may not be distributed whole or in any part to third parties.
 *
 * Copyright ©2019 Analog Devices, Inc. All rights reserved.
 */
#ifndef __I2C_BEEP_IC_1_H__
#define __I2C_BEEP_IC_1_H__

#include "SigmaStudioFW.h"
#include "i2c-beep_IC_1_REG.h"

#define DEVICE_ARCHITECTURE_IC_1                  "ADAU1701"
#define DEVICE_ADDR_IC_1                          0x68

/* DSP Program Data */
#define PROGRAM_SIZE_IC_1 5120
#define PROGRAM_ADDR_IC_1 1024
ADI_REG_TYPE Program_Data_IC_1[PROGRAM_SIZE_IC_1] = {
0x00, 0x19, 0x1F, 0x20, 0x01, 
0x00, 0x09, 0x08, 0x22, 0x01, 
0x00, 0x02, 0x01, 0xA0, 0x01, 
0xFF, 0xE1, 0x18, 0x22, 0x01, 
0x00, 0x02, 0x00, 0xA0, 0x01, 
0x00, 0x10, 0x00, 0xEA, 0x01, 
0x00, 0x20, 0x00, 0xF2, 0x01, 
0x00, 0x10, 0x00, 0xC0, 0x01, 
0x00, 0x00, 0x00, 0x00, 0x01, 
0xFF, 0xF0, 0x01, 0x21, 0x01, 
0x00, 0x00, 0x00, 0xA1, 0x01, 
0xFF, 0xE1, 0x08, 0x22, 0x41, 
0x00, 0x28, 0x00, 0xE2, 0x01, 
0x00, 0x20, 0x00, 0xC0, 0x01, 
0x00, 0x2F, 0xFF, 0x20, 0x01, 
0xFF, 0xE1, 0x08, 0x22, 0x01, 
0x00, 0x30, 0x00, 0xE2, 0x01, 
0x00, 0x32, 0x02, 0x20, 0x01, 
0x00, 0x00, 0x00, 0xE2, 0x01, 
0x00, 0x01, 0x08, 0x20, 0x01, 
0xFF, 0x68, 0x00, 0x02, 0x01, 
0x00, 0x00, 0x00, 0x00, 0x01, 
0x00, 0x00, 0x00, 0x00, 0x01, 
0x00, 0x00, 0x00, 0x00, 0x01, 
0x00, 0x00, 0x00, 0x00, 0x01, 
0x00, 0x00, 0x00, 0x00, 0x01, 
0x00, 0x00, 0x00, 0x00, 0x01, 
0x00, 0x00, 0x00, 0x00, 0x01, 
0x00, 0x00, 0x00, 0x00, 0x01, 
0x00, 0x00, 0x00, 0x00, 0x01, 
0x00, 0x00, 0x00, 0x00, 0x01, 
0x00, 0x00, 0x00, 0x00, 0x01, 
0x00, 0x00, 0x00, 0x00, 0x01, 
0x00, 0x00, 0x00, 0x00, 0x01, 
0x00, 0x00, 0x00, 0x00, 0x01, 
0x00, 0x00, 0x00, 0x00, 0x01, 
0x00, 0x00, 0x00, 0x00, 0x01, 
0x00, 0x00, 0x00, 0x00, 0x01, 
0x00, 0x00, 0x00, 0x00, 0x01, 
0x00, 0x00, 0x00, 0x00, 0x01, 
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
};

/* DSP Parameter (Coefficient) Data */
#define PARAM_SIZE_IC_1 4096
#define PARAM_ADDR_IC_1 0
ADI_REG_TYPE Param_Data_IC_1[PARAM_SIZE_IC_1] = {
0x00, 0x00, 0x00, 0xFF, 
0x00, 0x02, 0x58, 0xBF, 
0x00, 0x80, 0x00, 0x00, 
0x00, 0x00, 0x00, 0x00, 
0x00, 0x00, 0x00, 0x00, 
0x00, 0x00, 0x00, 0x00, 
0x00, 0x00, 0x00, 0x00, 
0x00, 0x00, 0x00, 0x00, 
0x00, 0x00, 0x00, 0x00, 
0x00, 0x00, 0x00, 0x00, 
0x00, 0x00, 0x00, 0x00, 
0x00, 0x00, 0x00, 0x00, 
0x00, 0x00, 0x00, 0x00, 
0x00, 0x00, 0x00, 0x00, 
0x00, 0x00, 0x00, 0x00, 
0x00, 0x00, 0x00, 0x00, 
0x00, 0x00, 0x00, 0x00, 
0x00, 0x00, 0x00, 0x00, 
0x00, 0x00, 0x00, 0x00, 
0x00, 0x00, 0x00, 0x00, 
0x00, 0x00, 0x00, 0x00, 
0x00, 0x00, 0x00, 0x00, 
0x00, 0x00, 0x00, 0x00, 
0x00, 0x00, 0x00, 0x00, 
0x00, 0x00, 0x00, 0x00, 
0x00, 0x00, 0x00, 0x00, 
0x00, 0x00, 0x00, 0x00, 
0x00, 0x00, 0x00, 0x00, 
0x00, 0x00, 0x00, 0x00, 
0x00, 0x00, 0x00, 0x00, 
0x00, 0x00, 0x00, 0x00, 
0x00, 0x00, 0x00, 0x00, 
0x00, 0x00, 0x00, 0x00, 
0x00, 0x00, 0x00, 0x00, 
0x00, 0x00, 0x00, 0x00, 
0x00, 0x00, 0x00, 0x00, 
0x00, 0x00, 0x00, 0x00, 
0x00, 0x00, 0x00, 0x00, 
0x00, 0x00, 0x00, 0x00, 
0x00, 0x00, 0x00, 0x00, 
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
};


/* Register Default - IC 1.CoreRegister */
ADI_REG_TYPE R0_COREREGISTER_IC_1_Default[REG_COREREGISTER_IC_1_BYTE] = {
0x00, 0x18
};

/* Register Default - IC 1.HWConFiguration */
#define R3_HWCONFIGURATION_IC_1_SIZE 24
ADI_REG_TYPE R3_HWCONFIGURATION_IC_1_Default[R3_HWCONFIGURATION_IC_1_SIZE] = {
0x00, 0x18, 0x08, 0x00, 0x00, 0x00, 0x00, 0x00, 0x00, 0x00, 0x00, 0x00, 0x00, 0x00, 0x00, 0x00, 0x80, 0x00, 0x00, 0x00, 0x00, 0x00, 0x00, 0x01
};

/* Register Default - IC 1.CoreRegister */
ADI_REG_TYPE R4_COREREGISTER_IC_1_Default[REG_COREREGISTER_IC_1_BYTE] = {
0x00, 0x1C
};


/*
 * Default Download
 */
#define DEFAULT_DOWNLOAD_SIZE_IC_1 5

void default_download_IC_1() {
	SIGMA_WRITE_REGISTER_BLOCK( DEVICE_ADDR_IC_1, REG_COREREGISTER_IC_1_ADDR, REG_COREREGISTER_IC_1_BYTE, R0_COREREGISTER_IC_1_Default );
	SIGMA_WRITE_REGISTER_BLOCK( DEVICE_ADDR_IC_1, PROGRAM_ADDR_IC_1, PROGRAM_SIZE_IC_1, Program_Data_IC_1 );
	SIGMA_WRITE_REGISTER_BLOCK( DEVICE_ADDR_IC_1, PARAM_ADDR_IC_1, PARAM_SIZE_IC_1, Param_Data_IC_1 );
	SIGMA_WRITE_REGISTER_BLOCK( DEVICE_ADDR_IC_1, REG_COREREGISTER_IC_1_ADDR , R3_HWCONFIGURATION_IC_1_SIZE, R3_HWCONFIGURATION_IC_1_Default );
	SIGMA_WRITE_REGISTER_BLOCK( DEVICE_ADDR_IC_1, REG_COREREGISTER_IC_1_ADDR, REG_COREREGISTER_IC_1_BYTE, R4_COREREGISTER_IC_1_Default );
}

#endif
