AravinthPanch/araBeat/images/audio/wondom-dsp-1.jpg

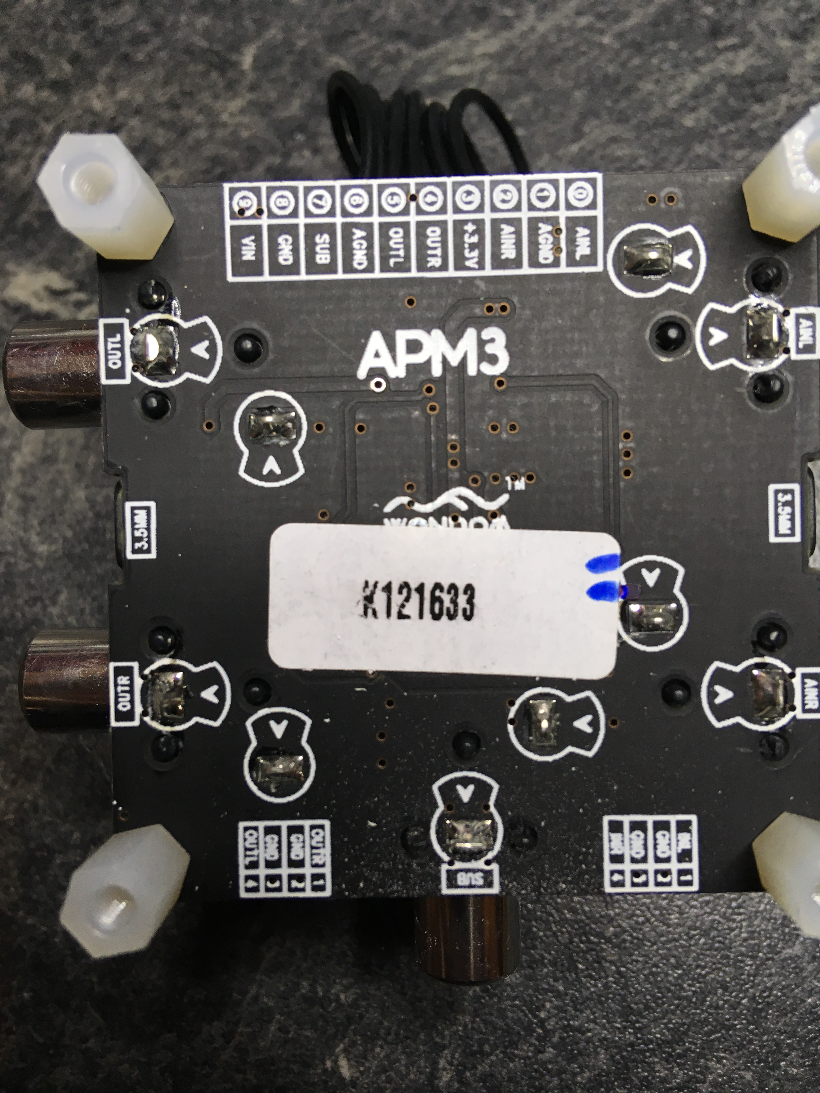
images/audio/wondom-dsp-1.jpg
