AravinthPanch/araBeat/images/audio/wondom-dsp-2.jpg

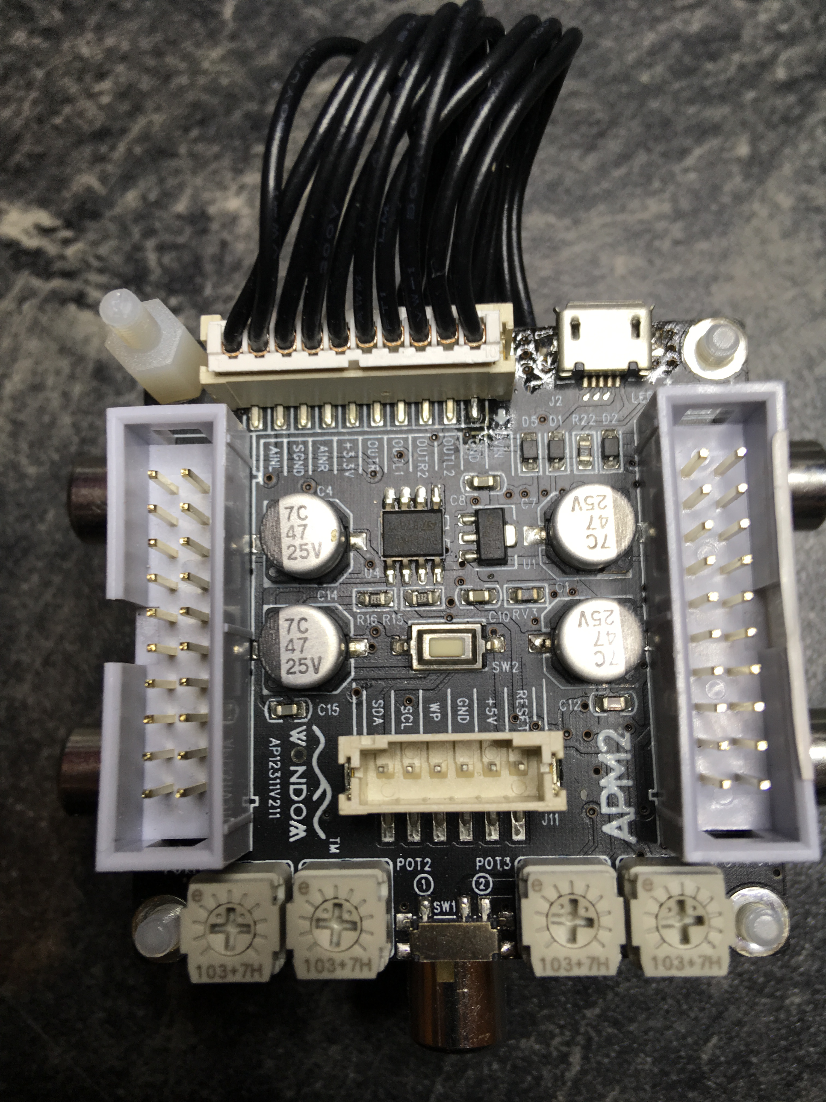
images/audio/wondom-dsp-2.jpg
