AravinthPanch/araBeat/images/audio/wondom-dsp-3.jpg

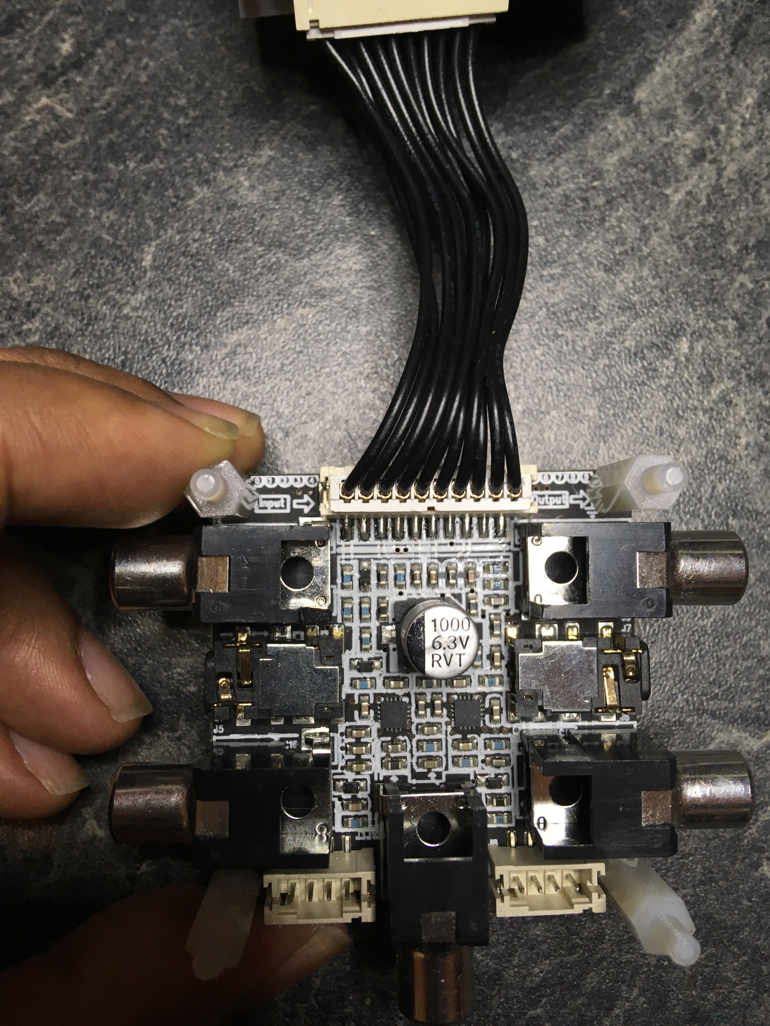
images/audio/wondom-dsp-3.jpg
