AravinthPanch/araBeat/images/final/2021-3-29-3.jpg

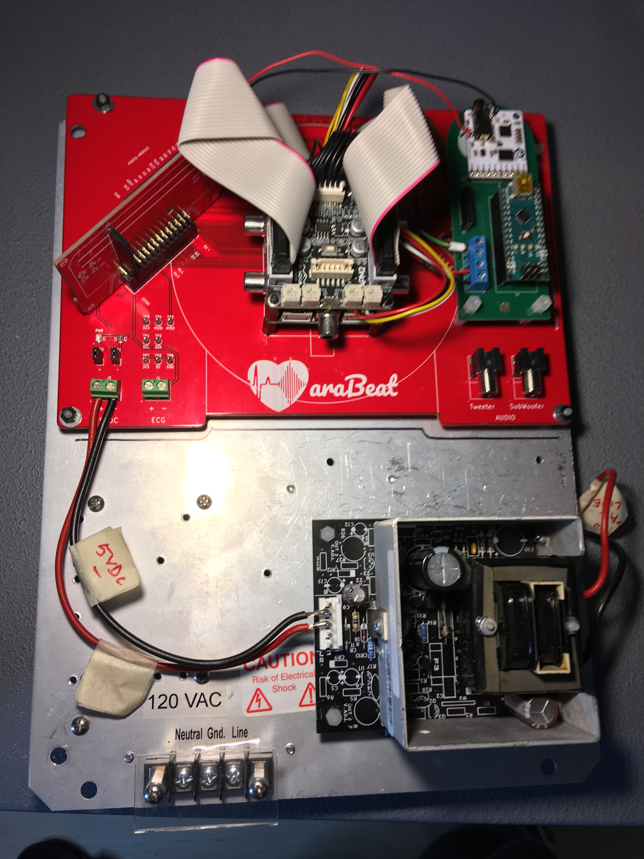
images/final/2021-3-29-3.jpg
