AravinthPanch/araBeat/images/final/2021-3-29-6.jpg

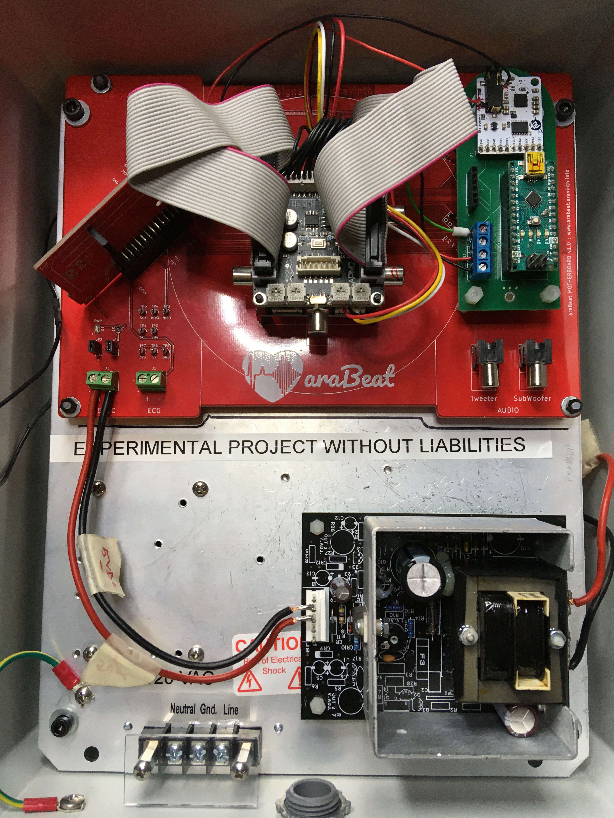
images/final/2021-3-29-6.jpg
