AravinthPanch/araBeat/images/final/2021-3-29-11.jpg

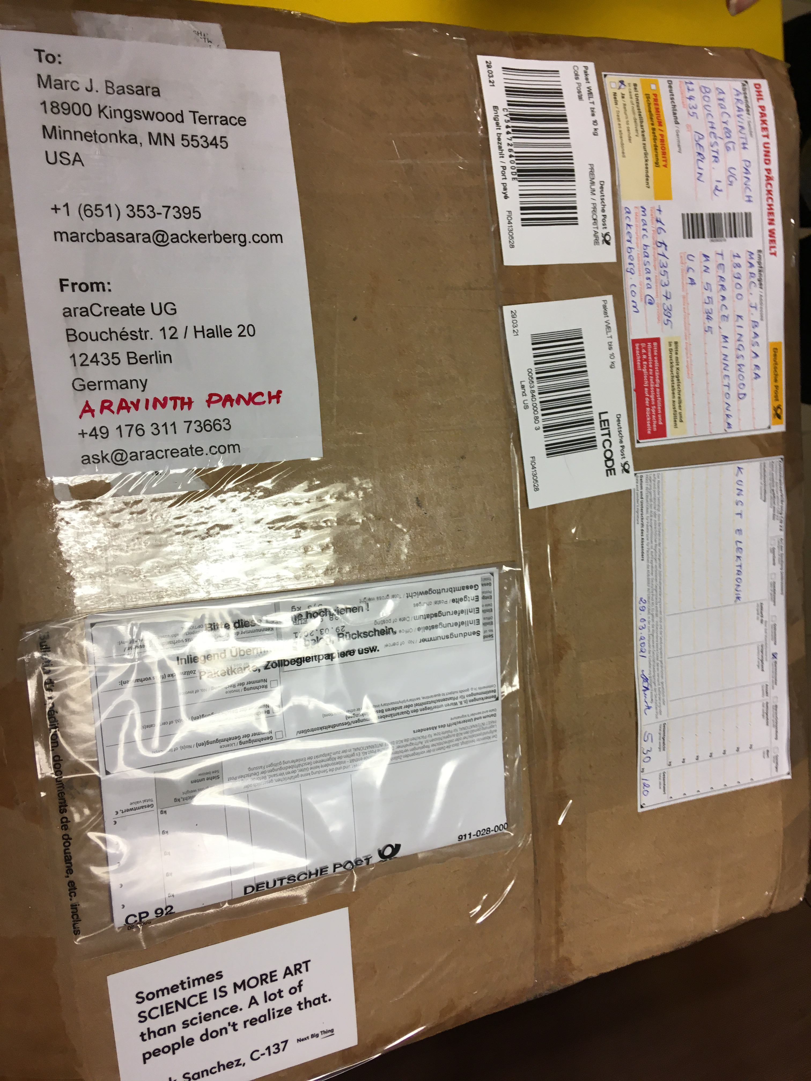
images/final/2021-3-29-11.jpg
